ibkickinit/schindler-clone/clockInfo.txt

-------------------------------------
| Tool Version : Vivado v.2025.2
| Date         : Sun Jun  7 10:25:25 2026
| Host         : justin-Yoga-7-14ITL5
| Design       : design_1
| Device       : xc7z020-clg400-1--
-------------------------------------

For more information on clockInfo.txt clock routing debug file see https://support.xilinx.com/s/article/000035660?language=en_US
