ibkickinit/schindler-clone/00-index.md

# Schindler 2.0 — 00 Index

**Status:** ACTIVE — HD pipeline development on Zybo Z7-20
**Type:** Personal venture
**Code location:** `_PROJECTS/Schindler-2.0/` (this folder, repo at root)
**GitHub:** `ibkickinit/schindler-clone` *(rename to `schindler-2` planned later)*

## What this is

FPGA-based hardware project to drive video to legacy CRTs at film cadences (24/30 fps), with the broader scope of acting as a general broadcast-grade HD signal processor. Spiritual successor to the Cal Media MVPHD-24 device — replicating that workflow with modern FPGA tech, and extending to HD pipeline + sync conversion + per-CRT color profiles + RF modulator (Pro) for period sets.

The mission: keep heritage display gear functional in modern production workflows, where 24fps cinema cadence needs to drive into displays designed for older signal standards.

## Two SKUs, one electronics design

**One internal electronics design — two packaging variants.** Mini and Pro share the same carrier PCB, the same TE0720 SOM, the same FPGA HDL, the same PetaLinux control plane. They differ in chassis form factor, front-panel hardware, rear-panel I/O complement, and carrier stuffing.

- **Mini v1** — first shipping SKU. Half-rack 1RU chassis. Mono OLED + tactile switches front panel. Subset of stuffing (no SDI, no RF modulator, no dual SYNC OUT, no per-connector LEDs, no rear LCD). Indicative retail $1,500–2,500; parts cost ~$572.
- **Pro v2** — full-rack 1RU chassis. NHD-2.9 color TFT + RP2040 + BT817Q EVE mezzanine front panel. Full silicon stuffing. Indicative retail $2,500+; parts cost ~$816. Gated on Mini selling.

See [`docs/packaging-skus.md`](docs/packaging-skus.md) for SKU stuffing matrix + chassis detail.

## Doc structure

- [`docs/01-spec.md`](docs/01-spec.md) — SSOT for internal electronics architecture and feature set. Applies to both SKUs.
- [`docs/packaging-skus.md`](docs/packaging-skus.md) — Mini vs Pro packaging differences (chassis, front panel, rear panel I/O, stuffing variants).
- [`docs/dev-roadmap.md`](docs/dev-roadmap.md) — SSOT for active development arc and deferred work. **Read this first** to know what's being built right now.
- [`docs/01-spec-changelog.md`](docs/01-spec-changelog.md) — dated decision history.
- [`docs/signal-flow.md`](docs/signal-flow.md) — Mermaid block diagrams (video signal path, sync subsystem, control plane).
- [`docs/panel-layout.md`](docs/panel-layout.md) — Pro panel layout. Mini layout in `packaging-skus.md`.
- [`docs/bom-v1.md`](docs/bom-v1.md) — BOM with Mini/Pro stuffing variants.
- [`docs/ui-menu.md`](docs/ui-menu.md) — Pro UI menu hierarchy. Mini UI hierarchy authored when Mini PetaLinux UI work activates.
- [`docs/mvphd-comparison.md`](docs/mvphd-comparison.md) — MVPHD-24 feature comparison + gap analysis.
- [`docs/rf-modulator-subsystem.md`](docs/rf-modulator-subsystem.md) — RF modulator detail (Pro feature).
- [`docs/opamp-stage.md`](docs/opamp-stage.md) — output op-amp design.
- [`docs/r2r-dac.md`](docs/r2r-dac.md) — R-2R DAC perfboard reference (Zybo bench).
- [`docs/schindler-playbook.md`](docs/schindler-playbook.md) — development narrative.
- [`docs/Hardware/`](docs/Hardware/) — archived future-evaluation hardware (Smart Artix, Smart Zynq SL, TE0712, TinyZynq) — **NOT** on the active dev path. Preserved for archival reference.

## Active development arc

Building **HD pipeline top-down** on Zybo Z7-20:

```
Phase A: HDMI passthrough        (next up)
Phase B: VDMA frame buffer
Phase C: Polyphase scaler
Phase D: Frame rate conversion
Phase E: Color pipeline
Phase F: Geometry warp
Phase G: Re-attach analog terminal encoders (Phase 2 HDL plugs back in here)
```

Migration from Zybo to TE0720 production target comes after the HD pipeline validates. See [`docs/dev-roadmap.md`](docs/dev-roadmap.md) for current status, deferred work, and forward-looking work.

## Recently completed

**Phase 2 first-light** on Zybo Z7-20 + R2R DAC perfboard:
- Monochrome NTSC composite at 24.000 fps exact — scope-validated
- `hdl/vid_timing.v` + `hdl/vbi_gen.v` + `hdl/sample_gen.v` validated
- `hdl/chroma_gen.v` written + integrated + builds clean; chroma burst bench verification deferred per HD-pipeline-first priority shift

## Hardware status

- ✅ **Digilent Zybo Z7-20** — active dev platform
- ✅ R-2R DAC perfboard + op-amp output stage
- ✅ Phase 2 NTSC composite HDL on bench, scope-validated through monochrome

**Inbound 2026-05-13:**

*Digilent order (Pmod accessories for Arty S7-25 ecosystem — FedEx 487403305746):*
- Pmod OLED 128×32 mono (410-222) — **Mini front-panel UI prototype**, exact display class as production
- Pmod OLEDrgb 96×64 color (410-323) — Pro UI flow / menu hierarchy prototyping at small scale
- Pmod ENC rotary encoder ×2 (410-117) — **Pro dual-encoder firmware prototyping**
- Pmod SWT 4 slide switches (410-083) — UI input testing
- Pmod R2R (410-165) — backup / cleaner R-2R DAC vs perfboard
- Pmod TPH2 test point header (410-135) — debug measurement
- Pmod Cable Kit + 6-pin splitter (240-021-2) — Pmod fan-out wiring
- Pmod VGA (410-345) — prototype platform for VGA OUT terminal if banked (currently in `01-spec.md` § 21 open questions)

*HelloFPGA order (China — bench eval / inventory):*
- Smart ARTIX Development Board V1.3 — inventory (archived in `docs/Hardware/SmartArtix/`)
- Smart ZYNQ 7020 Minimum System V1.3 (Smart Zynq SL) — inventory (archived in `docs/Hardware/SmartZynq/`)
- **LT8619C chips ×5** — production-quantity HDMI-input silicon stockpile
- LT8619C HDMI-to-RGB demo board — second LT8619C-EVB

*Pending order:*
- **Riverdi RVT43HLBFWN00** (4.3" 480×272 EVE4 intelligent display with BT817Q + flash on board, ~$62) — Pro mezzanine EVE toolchain dev platform. Replaces earlier ME817EV consideration; cheaper, more complete, matches production BT817Q spec exactly. Stock-pending at Mouser / DigiKey; not time-critical.

Net effect: enables a **parallel front-panel UI prototyping arc** on Arty S7-25 + Pmod OLED/OLEDrgb/ENC that doesn't block on Zybo HD pipeline phases A-G, and a parallel **EVE toolchain learning arc** once RVT43HLBFWN00 arrives.

**Future-evaluation hardware** (procured but NOT the active dev plan — bench eval / parts inventory only):
- Trenz TE0720-04-31C33MA SOM, TE0703-07 dev carrier, EVAL-ADV7393EBZ, LT8619C-EVB, ADV7280, ADV7393, LTC6912, AD9204, encoders, op-amps, BNCs (various 2026-05-10 / 11 procurements)
- Digilent Arty S7-25 — toolchain learning + Spartan-7 comparison only
- Smart Artix V1.3 / Smart Zynq SL V1.3 / TE0712-02 / TinyZynq — evaluation archive (`docs/Hardware/`)

The TE0720 is the **production-target SOM**; bench dev happens on Zybo Z7-20 (same Z-7020 silicon family). Production migration after HD pipeline validates.

## Operating principle (code in vault)

`.git/` syncs to Dropbox cloud. NEVER delete `.git/` from cloud — propagates to local and destroys repo. See `_PROJECTS/NovaTool/00-index.md` for full rationale on code-in-vault.

## Migration status

- [x] Migrated from `~/schindler-clone/` to `_PROJECTS/Schindler-2.0/` (2026-05-06)
- [x] Remote URL cleaned (no embedded PAT)
- [x] Two-SKU strategy banked (Mini v1 / Pro v2) (2026-05-12)
- [x] Doc tree consolidated: mini-spec + carrier-board absorbed into 01-spec; packaging-skus + dev-roadmap created (2026-05-13)
- [ ] Rename GitHub repo: `schindler-clone` → `schindler-2`
- [ ] Document FPGA-specific `.dropboxignore` patterns once active build artifacts appear

## Naming history

- Working title: `schindler-clone` (placeholder during initial setup)
- Final name: **Schindler 2.0** (chosen 2026-05-06; emphasizes spiritual successor framing rather than direct clone)
