ibkickinit/schindler-clone/docs/part-lock-2026-06-12.md

# Schindler 2.0 — Production Part-Lock Pull-Sheet (Pro)

**Generated:** 2026-06-12 · **Source of truth:** [`bom-v1.md`](bom-v1.md) (this is a flat procurement view of it — if they disagree, the BOM wins). Qty = **per Pro unit**; ×100 for the production run. Vendor assumed **DigiKey / Mouser** unless noted. Status: 📋 = locked, not yet ordered; ✅ = on order/received; 🔬 = bench eval.

## Active silicon

| Ref | MPN | Mfr | Qty | Pkg | Status |
|---|---|---|---:|---|---|
| Zynq SoM | TE0720-04-62I33MA | Trenz | 1 | SoM | 📋 |
| HDMI ESD/lvl ×2 | TPD12S016PWR | TI | 2 | — | ✅ |
| HDMI RX | LT8619C | Lontium | 1 | — | ✅ |
| Analog decoder | ADV7280AWBCPZ-M-RL | ADI | 1 | — | ✅ |
| Analog enc/DAC | ADV7393BCPZ-REEL | ADI | 1 | — | ✅ |
| Video buffers | LMH6643MAX/NOPB | TI | 3 | MSOP-8 | ✅ (2 out + 1 sync) |
| SDI RX (Pro) | GS3470 | Semtech | 1 | — | 📋 |
| SDI TX (Pro) | GS2962 | Semtech | 1 | — | 📋 |
| Genlock PGA | LTC6912CGN-2#PBF | ADI | 1 | — | ✅ |
| Genlock ADC | AD9204BCPZ-20 | ADI | 1 | — | ✅ |
| SYNC1 DAC | AD9742 | ADI | 1 | — | 📋 |
| Clock gen ×2 | Si5351A-B-GTR | Skyworks | 2 | MSOP-10 | 📋 (genlock + RF) |
| UI MCU ×2 | RP2040 | Raspberry Pi | 2 | QFN-56 | 📋 (genlock + mezz) |
| QSPI flash ×2 | W25Q128JVSIQ | Winbond | 2 | SOIC-8 | 📋 |
| Term switch | TS5A23159 | TI | — | — | 📋 (input/genlock) |
| Graphics ctrl | BT817Q | BridgeTek | 1 | — | 📋 |
| LED drivers | TLC59116F | TI | 3 | — | 📋 |
| WiFi/BT module | LWB5+ | Laird | 1 | module | 📋 |

## Power

| Ref | MPN | Mfr | Qty | Status |
|---|---|---|---:|---|
| IEC + filter + fuse | FN9260B-6-06 | Schaffner | 1 | ✅ |
| Mains fuse | 0213002.MXP (2 A T) | Littelfuse | 1 | 📋 |
| PSU | LRS-50-12 | Mean Well | 1 | ✅ |
| Protection eFuse | TPS26600 | TI | 1 | 📋 |
| Power monitor | INA226AIDGSR | TI | 1 | 📋 |
| Soft-power ctrl | LTC2954ITS8-1 (TSOT-23) | ADI | 1 | 📋 |
| 5 V / 3.3 V buck | LMR33640ADDAR | TI | 2 | 📋 |
| 1.2 V buck | TLV62568DBVR | TI | 1 | 📋 |
| 1.8 V analog LDO | TPS7A2018PDBVR | TI | 1 | 📋 |
| Clean analog POL LDO | ADP7142 (adj) | ADI | ~3 | 📋 (per ADC/decoder, sized at schematic) |

## Connectors

| Ref | MPN | Mfr | Qty | Status |
|---|---|---|---:|---|
| BNC 75 Ω R/A PCB | 73101-0120 | Molex | 14 | 📋 |
| HDMI Type A R/A | 10029449-001RLF | Amphenol ICC | 2 | 📋 |
| RJ45 Gig magjack | JXD1-0001NL | Pulse | 1 | 📋 |
| USB-C 2.0 R/A | USB4085-GF-A | GCT | 1 | 📋 |
| USB-C ESD | TPD4S014DBVR | TI | 1 | 📋 |
| RP-SMA bulkhead | CONREVSMA001 | Linx | 2 | 📋 |
| Antenna (dual-band) | ANT-DB1 | Linx | 2 | 📋 — verify vs LWB5+ grant |
| PSU header | 0039291028 (+ 5557-02R hsg) | Molex | 1 | 📋 |
| F-connector (RF bd) | 82-4421-RFX | Amphenol RF | 1 | 📋 |

## Panel / UX

| Ref | MPN | Mfr | Qty | Status |
|---|---|---|---:|---|
| Front TFT | NHD-2.9-376960AF-ASXP | Newhaven | 1 | 📋 |
| TFT backlight boost | TPS61040 | TI | 1 | 📋 |
| Rear LCD | NHD-1.5-240240AF-CSXP | Newhaven | 1 | 📋 |
| Encoders | EC11E18244AU | Alps | 2 | ✅ |
| Tactile buttons | PTS645SM43SMTR92LFS | C&K | ~7 | 📋 |
| Power button | E-Switch PV6 (illum. mom.) | E-Switch | 1 | 📋 |
| Status LEDs | L-3VEGW-CA (3 mm bi-color CA) | Kingbright | 21 | 📋 |

## RF daughter board (Pro)

| Ref | MPN | Mfr | Qty | Status |
|---|---|---|---:|---|
| AM modulator | ADL5391ACPZ-R7 | ADI | 1 | 📋 (bench 🔬) |
| RF amp | ERA-3SM+ | Mini-Circuits | 1 | 🔬 (5 on order) |
| Shield can frame | MS643-10F-NS | Masach | 1 | 📋 |
| Shield can cover | MS643-10C-NS | Masach | 1 | 📋 |
| Feedthrough (DC) | NFM21PC104R1E3D | Murata | 2 | 📋 |
| Feedthrough (I²C) | NFM21CC102R1H3D | Murata | 2 | 📋 |
| Series ferrite (opt) | BLM21PG600SN1D | Murata | 2 | 📋 |
| Output trims | 3224W (SMD multiturn) | Bourns | 2 | 📋 |
| RF ESD | PESD3V3L1BA | NXP | 1 | 📋 |
| (Si5351 + 25 MHz xtal, u.FL jack + cable, 6-pin header — see RF BOM) | | | | |

## Thermal / mechanical

| Ref | MPN / spec | Mfr | Qty | Status |
|---|---|---|---:|---|
| SoM heatsink | 33337 | Trenz | 1 | ✅ |
| Fan | NF-A4x20 PWM | Noctua | 1 | 📋 |
| SoM gap pad | silicone, ~1 mm | generic | 1 | 📋 |
| Chassis | 1U full-rack extruded | Hammond | 1 | 📋 (model at mech) |
| Front/rear panel | milled aluminum | Front Panel Express | 1 ea | 📋 (from `panel-layout.md`) |
| Standoffs / screws / M4 earth stud | M3 brass / M2.5 / M4 | generic | set | 📋 |

## Bulk passives (sized at schematic — not individually pre-locked)

- Decoupling: 0.1 µF + 10 µF per rail/IC (X7R / X5R).
- Input front-ends: BAV99 clamp + TVS, 75 Ω term, AC-couple + anti-alias R/C per CVBS/component/REF input.
- 12 V bulk: 3× Murata GRM32 22 µF 25 V X7R.
- RF bandpass: 5th-order Butterworth — Coilcraft 0805CS-class L + C0G C (~9 parts), values bench-tuned.
- 50→75 Ω MLP: 43 Ω + 82 Ω 1%; audio combiner: 3× R.
- LTC2954 timing (ONT/PDT) caps, PB R-C; eFuse OVP/UVLO/ILIM/dVdt resistor set.

## Still open (deliberate — not a part gap)

- **FCC emissions class** → defaulting **Class B** margin; relax to A only if filter margin wanted. Pre-layout call.
- **Antenna final MPN** → confirm Linx ANT-DB1 against the LWB5+ FCC grant antenna list before order.
- **Production knob** → post-UX-eval; shaft-mount, no netlist impact.
- **Procurement-final suffixes** → BNC packaging tray/reel, E-Switch PV6 color/voltage, at order time.
