ibkickinit/schindler-clone/docs/warp-engine-real-geometry-findings.md

# Warp engine — real-geometry findings (the TB green does NOT mean real-time at 1080p)

> **RESOLVED 2026-06-07 — the warp engine is now real-time at 1080p.** Three enhancements (below)
> close the gap; `pg_warp_real_tb` (8-way/NTILE=1024, PD=DREQ=64, LEAD=32768) clears rot20/shrink/aniso
> with underruns=0 over the full 1280×720 frame; rot45 has a single cold-start underrun (cn=3, benign).
> No dual-clock fill. **The resolution is in §"Resolution" at the bottom; the analysis below is the
> investigation that found the bottlenecks.**

**Date:** 2026-06-07. **Re:** confirming the real-time LEAD at the production geometry before sizing
cache ways (the "confirm the real lead first" decision).

**TL;DR:** I built a full real-geometry gate (`sim/pg_warp_real_tb.v`, 1280×720 ← 1920×1080, 720p60
raster) and ran shrink 1.5× (the fill/lead driver). **It is NOT real-time** as architected — and the
reason is not the fill rate. The TB (`pg_warp_dma_tb`, 1/5 scale) passes 4/4 because its small frame
fits the cache entirely and gets a disproportionate V-blank warmup head-start; **neither holds at full
scale.** Two real bottlenecks the TB masked: **(1) no LRU eviction**, and **(2) prefetch feed depth.**

## The measurements (real geometry, shrink 1.5×, collected of 921600)

| cache | PD / DREQ | LEAD | collected | note |
|---|---|---|---|---|
| 4-way / 512 | 16 / 16  | 8k–49k | **5%** | LEAD has no effect; capacity-bound |
| 16-way / 2048 | 16 / 16  | 16k–131k | **25%** | LEAD still no effect; PD-bound |
| 16-way / 2048 | 64 / 64  | 65k | 23% | deeper PD *worse* — still evicting |
| 16-way / **16384** (no eviction) | 16 / 16 | 65k–262k | **62%** | eviction removed → big jump |
| 16-way / 16384 | 64 / 64  | 131k | **85%** | now PD/lead start working |
| 16-way / 16384 | **128 / 128** | **262k** | **94%** | trending to real-time, impractical cost |

Fill-path health at the stalling point (16-way/2048, PD16, LEAD65k): **clk/tile = 96 (= the target 2.67
px/clk — the gap-free fill is at its design rate), but beat_duty = 0.20, work_frac = 0.34** (the DMA has
a pending fetch only 34% of the time). So the DMA is *starved*, not slow.

## Why — two coupled bottlenecks the small TB hid

1. **No LRU eviction.** My victim is free-way-first with a round-robin fallback only when a set is
   *full*. That never *proactively* recycles dead tiles — they sit valid until the set fills, then RR
   evicts arbitrarily (sometimes a still-live tile). The TB never hit this (its frame fits the cache, so
   eviction never happens). At 1080p, shrink touches ~8100 tiles while its *live* working set is only a
   few hundred; with LRU + worst-set-live ≤ ways, a modest cache would hold the live set indefinitely
   and never evict a live tile. Without it, the cache fills with dead tiles and thrashes — which is why
   "no eviction" (NTILE=16384) jumped shrink 25%→62%, and why more ways = more rows-before-stall.

2. **Prefetch feed depth.** Even with eviction removed, PD=16 caps shrink at 62%; PD=128 + a very deep
   lead reaches 94%. The fill is serial (tile_dma fills one tile at ~96 clk), so covering shrink's
   ~120-tile tile-row-crossing burst needs many fills queued and a deep lead to pre-fill it. The TB's
   24-tile burst hid this (16 sufficed). The *rate* is adequate (2.67 px/clk × frame ≈ 3.3M px ≫ the
   2.07M px shrink reads/frame, 1.6× headroom) — the problem is keeping the DMA continuously fed, which
   the current lead-gated race-then-idle prefetch does not.

## What this means

- **The reviewer's bet (2.67 px/clk + non-thrashing cache + deep lead) holds on *rate* but the
  "non-thrashing cache" needs real LRU, not RR**, once eviction is mandatory (it never is in the TB).
  And the prefetch needs more pacing/depth than the TB implied.
- **Dual-clock fill is probably still NOT the answer** — the rate has 1.6× headroom; the loss is feed +
  eviction, not bandwidth. Halving fill time would ease the burst-lead pressure but doesn't fix the
  underlying feed/eviction inefficiency.

## Recommended next architecture step (for discussion before building)

1. **Per-set tree-PLRU** victim (4/8-way). With worst-set-live ≤ ways, PLRU never evicts a live tile →
   a modest cache (NTILE 512–1024) holds shrink's live working set with no thrash. This is the big one.
2. **Re-measure the real-time lead/PD with PLRU** — expect the impractical PD=128 / 200-row-lead to drop
   sharply once the cache stops thrashing, because the prefetch no longer wastes fills re-fetching
   evicted tiles. Only then size ways (8-way for rot20's lead-aware 5–7, per
   `tools/warp_lead_assoc.py`).
3. If PLRU + reasonable PD still can't feed the DMA continuously, revisit prefetch pacing (issue rate
   matched to fill capacity) before reaching for dual-clock fill.

## Status of the assigned fill rework

The fill rework itself is **done and correct** — `pg_warp_dma_tb` passes all four transforms
(underruns=0, bit-err=0), the gap-free fill hits 96 clk/tile, multi-outstanding works. What this
real-geometry gate adds is: **the TB is necessary but not sufficient** — it cannot exercise eviction or
the full-scale burst, and both bite at 1080p. The cache (`pg_tilecache_rt2`) now takes a `WAY` parameter
(4 default, plumbed through `pg_warp_engine`) so the PLRU + 8-way work has a clean home, and
`pg_warp_real_tb.v` is the gate to drive it.

## Resolution (2026-06-07) — three enhancements make it real-time at 1080p

Each was found by the measurements above, applied in order, and re-swept on `pg_warp_real_tb`:

1. **FIFO-by-fetch eviction** (`pg_tilecache_rt2`, replaces RR fallback). Per-slot fetch-sequence
   stamp; the victim is the **oldest-fetched non-reserved** way (free-way-first, then FIFO). Because the
   prefetch fetches in the consumer's future-access order, the oldest-fetched resident tile is the one
   the consumer already passed = dead. A modest cache now recycles dead tiles continuously instead of
   filling up and thrashing. **Real-geometry shrink at 4-way/512: 5% → 62%.** No per-access update
   (FIFO ≈ LRU for the streaming prefetch order), so it's cheap.

2. **Wide gearbox** (`pg_tile_dma`). The receiver drained ≤3 px/clk with `beat_ready=nbits<=64`; since
   64b/beat isn't a multiple of 24b/px, the accumulator settled at a low equilibrium where `navail` was
   usually 2, throttling the beat rate to ~1.6 px/clk (`duty_when_work=0.60`) — just under shrink's
   ~1.67 px/clk need (hence the 94% ceiling). Fix: 4 px/clk drain + permissive `beat_ready=nbits<=96`
   (200-bit acc) so `navail` stays 3–4 and the receiver sustains the full 2.67 px/clk. **This is what
   took shrink from 94% to 100%** and dropped the PD need from 128 to 64.

3. **Deeper feed** — `PD` is now a parameter (default 16, **64 for the real geometry**) with matching
   `DREQ`. Keeps the DataMover continuously fed across the bursty miss pattern (the ~120-tile tile-row
   crossing). `work_frac` 0.34 → 1.00.

### Validated production config (real geometry)

| param | value | why |
|---|---|---|
| WAY | **8** | lead-aware worst-set-live ≤8 at LEAD=32768 (rot20=7, aniso=6); 4-way thrashes |
| NTILE | **1024** | 8-way × 128 sets (keep 128 sets — the hash needs them; ~96 RAMB36) |
| PD / DREQ | **64** | covers the ~120-tile crossing burst feed (PD=16 caps at 62%, 32 at ~80%) |
| LEAD | **32768** | shrink real-time needs it; 8-way still holds (max worst-set-live=7). 65536 pushes aniso to 9 → would need 16-way |
| victim | FIFO-by-fetch | non-thrashing eviction |
| gearbox | 4 px/clk / nbits≤96 | sustains 2.67 px/clk |

**LEAD is the binding cross-constraint:** shrink wants it deep, aniso's lead-aware count grows with it.
LEAD=32768 is the sweet spot where shrink is real-time AND all four stay ≤8-way. (rot45's lone cn=3
cold-start underrun is a warmup transient — the cache persists across frames in the genlocked system, so
it occurs at most once at power-on, on the top-left pixel.)

### Cost vs the small-TB config
- Cache BRAM ~2× (NTILE 512→1024). Pending/request FIFOs PD/DREQ 16→64 (logic, not BRAM). Wider gearbox
  acc (136→200b) + FIFO seq array (NTILE×16b) — modest.
- **No dual-clock fill** (the reviewer's hoped-for outcome): the 2.67 px/clk rate is sufficient once the
  gearbox actually sustains it and eviction stops wasting fills.

### Still open
- rot45 cold-start pixel (benign; could be cleaned with cross-frame prefetch warmup in firmware).
- The PD=128 regression (collapses vs PD=64) is unexplained — irrelevant since 64 is the operating
  point, but worth understanding before pushing PD higher.
- FIFO ≈ LRU holds for streaming/rotation here; a pathological revisit pattern could want true LRU. Not
  observed in the four transforms.

### Cold-start is power-on-once (not per-coeff-change) — confirmed by HDL inspection
The cache (`pg_tilecache_rt2`) has **no `sof`, no flush, no invalidate-all**: `vld` is cleared only
per-slot on evict and set per-slot on fill. `sof` resets only the prefetch's `lead_cnt` (benign — with a
warm cache the prefetch re-establishes its lead through hits, no refetch). Coeffs latch frame-atomically
inside `pg_affine`; on a live geometry change the FIFO age (global `fseq`) recycles the old-geometry
tiles as the new working set arrives — a smooth working-set shift, **not** a cold-start. So the rot45
cn=3 transient occurs at most once at power-on/reset, on the top-left pixel — it does NOT recur per frame
or per zoom/rotate/pan adjustment. (A very large single geometry jump could cost a one-frame transient as
the whole working set turns over, but not a persistent twinkle during incremental tuning. A mid-stream
coeff-change sim would be the definitive confirmation — good follow-up.)

### Timing: pending-availability cone collapsed from PD-deep to associativity-deep
The multi-outstanding pending check was refactored from a PD(64)×4 = 256-comparator FIFO scan to a
single `(vld||rsv)&&tag` lookup over a set's WAY ways (write the tag at ISSUE with rsv=1, so resident
and in-flight are the same lookup): **WAY(8)×4 = 32 comparators**, bounded by associativity not lead
depth, and it scales if PD grows. Removes the cone rather than pipelining it. Both gates re-verified
identical. The consumer gather tag lookup (the original in-context WNS −3.5 path) is now 8-way; the build
will say whether it needs the reserved tag-lookup pipeline stage.

## Fit (2026-06-07) — 8-way/1024 does NOT fit the 7020; per-geometry LEAD does

The in-context build at the real-time config (8-way / NTILE=1024) **synthesized but failed impl DRC on
resource over-utilization, not timing**: `pg_re_0` (the warp engine) alone = **192 RAMB36 > 140
available**; total LUT 72580 / 53200. The cache is 4 banks × NTILE·64 × 24b; at NTILE=1024 that is
192 RAMB36 by itself. **The production target (TE0720) is also a Zynq-7020** (−2 silicon, same 140 BRAM)
— so 8-way/1024 fits neither the dev board nor the product. Removing the debug ILAs (~32 BRAM) is not
enough.

**Root of the 8-way requirement, and the fix.** 8-way came from the lead-aware worst-set-live at a
*single global* LEAD=32768 (rot20=7, aniso=6). But rot20 and aniso don't *need* a deep lead — only
downscale (shrink) does. A deep global lead over-inflates the easy transforms' per-set occupancy. With a
**per-geometry LEAD** — the firmware sets a shallow lead for rotation and a deep one for downscale —
every transform is real-time at a lead where worst-set-live ≤ 4 (validated on `pg_warp_real_tb`,
generous cache so capacity isn't the variable):

| transform | minimal real-time LEAD | worst-set-live @ that lead |
|---|---|---|
| rot20 | 1280 | 4 |
| rot45 | ~4096 | 2 |
| shrink 1.5× | 24576 | 3 |
| aniso (rot30+1.5×H) | ~10240–12288 | 4 |

Max worst-set-live across the per-geometry leads = **4 → 4-way / NTILE=512 (~96 RAMB36) fits the 7020.**
The cache only ever sees one transform's pattern at a time (at that transform's lead), so the global
lead-aware table that demanded 8-way no longer applies.

**LEAD must become a runtime register** (firmware-written per geometry, deep ∝ downscale factor) instead
of a build parameter — a small follow-up (the engine already takes LEAD as a param; expose it as a
GPIO-driven port). Cache persistence + frame-atomic coeff latching mean changing LEAD with the geometry
is a smooth working-set shift (same as the cold-start analysis above). Until then, a single fixed LEAD
will thrash whichever transform's lead it doesn't match at 4-way.

**Build status:** BD config set to 4-way/NTILE=512/PD=64/DREQ=64 (LEAD placeholder); rebuilding to confirm
the device holds the warp engine (BRAM ✓ expected ~96, LUT TBD) and timing closes. Per-geometry LEAD is
the remaining real-time mechanism (firmware).

### Cost ledger (4-way/512, the fitting config)
- Cache ~96 RAMB36 (4 banks × 512·64 × 24b). Fits 140 with room for VDMA/scaler/output once debug ILAs
  are dropped.
- LUT: 8-way build was 72580 (36% over). 4-way halves the lookup/vict/availability/seq logic; PD=64
  FIFOs + wide gearbox unchanged. Rebuild will say if it now fits 53200.
- No dual-clock fill. Single DataMover. Set-index unchanged.

### Fit round 2 (4-way/512): BRAM clears, now SLICES (LUT/FF) over by ~24%
4-way/NTILE=512 cleared the BRAM wall (cache ~96 RAMB36, no BRAM DRC error). Impl now fails at **place**
on slices: **13456 required / 10893 available (~24% over)** — LUT/FF, still not timing. Per-IP LUTs
(synth OOC):
- `pg_re_0` (warp engine) = **29723 LUTs** — dominant. PD=64/DREQ=64 FIFOs, the 200-bit wide gearbox
  (variable barrel shifters), the 512×16b `seq` array + 4-way age-argmax, the `(vld||rsv)&&tag`
  availability (4×4×24b), 2× affine DDAs, bilinear, `setf` multiplies.
- 3 system ILAs = ~10549 LUTs (`ila_s2mm_axi` 5218 + `ila_scaler_out` 2799 + `ila_mm2s_out` 2532),
  plus `ila_pixclk`/`ila_refclk` — **all debug-only.**
- VDMA 2982, scaler mem 2297, v_tc_rx/tx 1522/1327, etc.

**Closing the ~2563-slice gap (well-scoped, next session — verify each with a rebuild):**
1. **Drop the debug ILAs** (gate the `system_ila` cells + their probe nets behind an `ILA_EN` flag in
   `build_phase_b.tcl`, default off for warp builds): ~10549+ LUT ≈ ~1300–1500 slices. Closes roughly
   half. Low risk but touches the BD (must remove probe connections cleanly).
2. **PD/DREQ 64→32** if shrink real-time tolerates (re-check on `pg_warp_real_tb`): halves the pf_slot
   (64×9b) + tile_dma rq (64×24b) FIFOs.
3. **Trim `seq` width** 16→~10 bits (age only needs to order the live working set) and/or move it to
   LUTRAM/BRAM: saves ~512×6 FFs off the slice count.
4. If still short, narrow the gearbox barrel shifters (the 200-bit acc / variable 96-bit shifts are
   LUT-heavy) — but the wide gearbox is load-bearing for shrink's 2.67 px/clk, so re-verify real-time.

ILAs (1) + PD↓ (2) + seq↓ (3) should clear ~24% comfortably. None affects the validated datapath/
real-time behaviour; they're area trims + debug removal. After a clean place, read post-route WNS.

## Fit round 3 (4-way/512 + NO_ILA): FITS and routes — but WNS −28.76 (prefetch cone)
Gating the 3 debug ILAs (NO_ILA=1) recovered enough slices: the 4-way/NTILE=512/PD=64 warp build
**places, routes, and writes a bitstream on the 7020** (BRAM ✓ ~96, slices ✓). WHS=+0.0096 (hold ok).
But **WNS = −28.757 ns** at the 74.25 MHz pixel clock (13.468 ns period).

**Failing path (single dominant cone):**
`pg_re_0/.../u_tc/px__reg` (prefetch coord) → `u_tc/tag_reg[241]` (tag write). **41 logic levels, 41.5 ns**
(logic 10 ns / route 31.5 ns), CARRY4=11 (the `setf` `*13`/`*7` multiplies) + 12×LUT6 + MUXF7/8. This is
the **entire prefetch issue decision computed combinationally in one cycle**: px_ → ppx/ppy neighbours →
`setf`/`tidf` for 4 tiles → `(vld||rsv)&&tag` availability over the ways → first-unavailable select →
`vict` age-argmax → `ua_slot` → tag/slot write. The earlier in-context −3.5 was this same cone at 4-way
*without* the tag-at-issue + FIFO-vict additions; those (correct, and needed) deepened it to 41 levels.

**Fix (next session — the prefetch has slack, leads the consumer by LEAD, so pipeline latency is free):**
Pipeline the prefetch issue path into ~3–4 register stages, e.g.
 1. px_ → register ppx/ppy (4 neighbour coords) + their `setf`/`tidf` (the multiply — isolate it).
 2. register the `(vld||rsv)&&tag` availability result (av00..av11) per tile.
 3. register all_av + the first-unavailable `ua_*` (set/way/tid) selection (incl. `vict`).
 4. issue (tag/rsv/pf write).
**Hazard:** with pipeline latency, a tile issued at cycle T is not visible in the tag/rsv arrays for k
cycles, so cycles T+1..T+k could re-issue it (the same class as the original pend_has bug). Add a small
"recently-issued" bypass — a k-deep register of the last ua_slot/ua_tid checked in the availability —
or stall the coord-advance until the issue retires. The consumer gather lookup (looka→baddr→BRAM) is a
*separate*, shorter path and was not the worst; check it after the prefetch is pipelined.

Note the path is **76% route** (31.5 of 41.5 ns) — 41 logic levels scattered across the die. Pipelining
cuts both the logic depth and the routing (shorter nets per stage). This is careful hazard-prone work;
recommended for a fresh session per the build/WNS boundary.

**State at handoff:** fit + real-time both solved (all four real-time at 4-way/512 with per-geometry
leads: rot20@1280, rot45@4096, shrink@24576, aniso@12288 — rot45 1 cold-start px). Bitstream exists but
is non-functional at speed until the prefetch cone is pipelined. Build log: build_logs/warp_build_noila.log.

### Next-session pipelining plan (REFINED — feedforward vs state-dependent split)
The 41-level cone is two different animals; only one is hazard-prone. Do them in this order:

**1. Pipeline the FEEDFORWARD PREFIX first — hazard-free, biggest level reduction.**
   prefetch coord (px_) → ±1 neighbour coords → `setf` `×13`/`×7` multiplies → set indices + tile-ids
   (ps00..11, pt00..11). This depends ONLY on the coords (the affine DDA produces them deterministically
   ahead of time), touches no mutable cache state, so register it into ~3 stages with **zero re-issue
   hazard**. This is probably the bulk of the 41 levels (the two multiplies + neighbour math, CARRY4×11).
   Keep `lookup → reserve → write` as a single ATOMIC cycle.

**2. Re-time. If the atomic suffix now closes in one cycle, you are DONE — no hazard work at all.**
   Because the reservation still happens in the same cycle it reads state, the next prefetch coord sees
   it. Most likely outcome once the multiplies are staged out.

**3. ONLY IF the atomic suffix is still too deep, split it — "reserve immediately, compute pipelined":**
   - The `rsv` slot-reservation bit MUST be set combinationally at issue so it is visible next cycle —
     that single-cycle reservation prevents BOTH double-issue AND double-victim (two fills racing for one
     slot — the nastier corruption).
   - Pipeline only the heavy compute behind it (availability read, first-unavailable select, `vict`
     age-argmax).
   - Add a small **k-deep recently-issued shift-register (k≈4), checked combinationally** = a k-entry CAM
     covering the read-side shadow (the k cycles where a just-issued tile isn't yet in the arrays). This
     is far cheaper and safer than a coord-advance stall — a stall would throttle the prefetch and risk
     reintroducing the lead/starvation just solved.
   - **Re-run BOTH sim gates** after this — `pg_warp_dma_tb` (underruns=0, bit-err=0) AND
     `pg_warp_real_tb` (real-time, no re-issue starvation) + the lead-aware check. This re-verify is the
     part that must not be done tired.

Then: check the consumer gather path (looka→baddr→BRAM — separate, shorter) timing; rebuild; read WNS.

### ⚠️ NO_ILA is a load-bearing build constraint
The warp build fits the 7020 **only with the 3 debug ILAs gated off** (`NO_ILA=1`). Carry this into
bench/debug: you lose on-chip ILA visibility (scaler_out / mm2s_out / s2mm_axi pixel-stream capture)
exactly in the warp build where you might want it. If ILA visibility is needed for a warp bench session,
something else must give (smaller cache for that debug build, or fewer ILA slots).

### Bitstream status
`build_logs/warp_build_noila.log` produced a routed bitstream, but with WNS −28.76 it is **NON-FUNCTIONAL
at 74.25 MHz — do not bench it.** It only proves fit (place+route+BRAM+slices). A functional bitstream
needs the prefetch pipelining above + a clean WNS≥0 build.

### Fit round 4 (prefetch feedforward pipelined): WNS −28.76 → −20.27, suffix is the residue
Step 1 (register the feedforward — neighbour coords + setf *13/*7 multiplies into stage 2, suffix atomic;
commit `<feedforward>`) moved WNS from −28.76 to **−20.27** and is sim-verified (small TB 4/4 bit-exact;
real-geometry shrink@24576 / aniso@12288 / rot20@1280 real-time). New worst path:
`u_tc/ps01_reg → u_tc/tag_reg`, **32 logic levels / 33.3 ns (CARRY4=7, LUT6=9, MUXF7×4/MUXF8×2), 78%
route.** The setf is gone (source is the registered ps). The residue is the state-dependent SUFFIX:
`ps(reg) → (vld||rsv)&&tag availability over WAY ways → first-unavailable select → vict age-argmax →
tag/rsv write`.

**To close the remaining ~20 ns (next session — the hazard-prone part):**
1. **Replace the `vict` age-argmax with an O(1) per-set FIFO victim pointer.** `rr_set[NSET]` (WAYW bits/
   set) advanced on each rr-victim issue ≈ FIFO-per-set (rr naturally fills empty ways 0..WAY-1 first,
   then evicts oldest). Must still skip reserved (in-flight) ways to avoid double-victim. Removes the
   CARRY4×7 (the 16-bit fseq−seq subtracts) AND frees the 8192-FF `seq[512]×16b` array. Re-verify BOTH
   gates — it changes the eviction policy from global-FIFO to per-set-RR (should be equivalent for the
   streaming prefetch order, but prove it: underruns=0, bit-err=0, real-time).
2. **Then PIPELINE the suffix** (32 levels, 78% route, won't close by logic-trim alone — need ~10
   levels/stage). Split into ~3 stages with the agent's rule: keep the **`rsv` reservation combinational/
   immediate at issue** (victim now O(1) so the slot is known same-cycle the set is) and pipeline only
   the availability read behind a **k≈4 recently-issued shift-register checked combinationally** (a
   k-entry CAM) to cover the read-side shadow (cycles where a just-issued tile isn't yet in the arrays).
   This is the re-issue/double-victim hazard junction — re-verify both gates after.
3. Then check the consumer gather path (looka→baddr→BRAM, separate/shorter). Rebuild, read WNS.

Progress so far is monotone and sim-clean; the finish is careful hazard work. WHS healthy (+0.03).

### Fit round 5 (per-set RR victim): WNS −20.27 → −15.38, root cause = dynamic-addressed array reads
Per-set FIFO victim pointer (commit `<per-set-rr>`) removed the age-argmax: WNS −20.27 → **−15.38**,
CARRY4 11→2. Sim-verified (small TB 4/4; real-geom shrink/aniso/rot20 real-time). New worst path:
`u_tc/ps00_reg → u_tc/rr_set_reg`, **31 levels (LUT6=15, MUXF7=8, MUXF8=4, CARRY4=2), 76% route.**

**Root cause of the residue:** the tag/vld/rsv arrays are read at the COMPUTED slot `{ps, way}` — a
512-entry (NTILE) mux each (the MUXF7/8 cascade). The prefetch availability does 16 such reads
(4 tiles × WAY) and `vict` does WAY more; the chain `ps → array-read mux → compare → ua → vict →
ua_slot → tag/rsv/rr write` is the cone. Logic-trimming is exhausted (CARRY4 already gone); it must be
PIPELINED, and the array-read muxes are the deep part.

**Remaining closure (next session — multi-stage, careful):**
1. **Quick win first:** narrow `TIDW` 24→16 (tidf only uses {py[11:4],px[11:4]} = 16 b). Shrinks every
   tag mux + compare ~33% and the tag array. Low risk; re-verify gates.
2. **avm-snapshot (hazard-free) — the main lever.** Read each coord's 4-tile availability ONCE at
   coord-load (the deep array-read mux, pipelined into a registered 4-bit `avm` mask), then run the
   issue loop off `avm` + a local "issued" mask (set as tiles are reserved). This removes the array
   reads from the per-cycle issue loop entirely. It's hazard-free: coords process serially, so the
   snapshot + local updates are exact (no other coord issues mid-processing; prior issues are committed
   before s2_adv). Needs a 3rd prefetch stage (coord → ps/pt → avm+issue) with its own valid bit.
3. **Pipeline `vict`'s array reads** if it's then critical (it reads vld/rsv[{ua_set,way}] for the
   free-way scan): register the free-way/rr decision, or maintain a per-set "has-free-way" + the rr
   pointer incrementally so vict is a pure register read.
4. Rebuild; if still short, register the tag/vld/rsv READ itself (1-cycle) with the 1-entry
   current-issue bypass (issues commit to arrays in 1 cycle, so a 1-deep bypass covers the shadow).
Then check consumer gather; read WNS.

Progress this session: WNS −28.76 → −20.27 (feedforward pipeline) → −15.38 (per-set RR), monotone, each
step committed + both sim gates green. The finish is multi-stage prefetch pipelining (the array-read
muxes) — careful, re-verify-heavy, recommended fresh. WHS healthy throughout (+0.02).

### avm-snapshot design subtlety (resolved on paper — the key note for the fresh session)
Working the avm-snapshot through, the naive version DOESN'T work, for a non-obvious reason — document
this so it isn't re-discovered the hard way:
- **Compute avm combinationally each cycle** → the deep array-read mux is back on the path (the thing
  we're removing). No good.
- **Compute avm once at coord-LOAD into stage C** → 1-cycle bubble per coord. Fatal: hit-coords then
  take 2 cycles → prefetch advances ~0.5 coord/cycle < the consumer's ~0.78 (active fraction) → the lead
  erodes → starvation. (Verified by reasoning, not yet sim.)
- **Precompute avm one stage early (stage B, while stage C processes the current coord)** → STALE:
  adjacent coords SHARE tiles, so a tile coord-C reserves between the snapshot (T_b) and when coord-D
  is processed (T_c) is missed by avm(D) → D re-issues it → double-issue / wasted fetch / starvation.

**Resolution = the CAM bypass after all:** precompute avm in stage B, but OR-in a k-deep "recently
issued" list (the ua_tids issued since the snapshot) when loading stage C — `avm(D) =
precomputed_avail(D) | (D-tile ∈ recently_issued)`. k covers the issues in the snapshot→process window
(the current coord's ≤WAY issues + a margin; k≈WAY+2). This is the hazard junction the agent flagged;
it must be sim-verified (both gates) with attention to the shared-tile case (adjacent coords, and the
2×2 neighbour overlap within a coord). So the honest path is: **avm-snapshot (stage B precompute) +
k-deep recently-issued CAM bypass**, then pipeline vict, then re-time. Not a quick step — a careful
stateful pipeline with a real correctness hazard (double-issue via stale availability).

### ★ LEAD next-session step (CONFIRMED): the 512:1 mux is a STORAGE-SHAPE artifact, not inherent
Confirmed against source: `tag`/`vld`/`rsv` are declared `reg [..] x[0:NTILE-1]` (flat, 512 entries) and
read everywhere at the full slot `{set,way}` (e.g. `tag[{ps00,aw}]`, `vld[{st,w}]`) → a 9-bit dynamic
address → the 512:1 mux that IS the −15 ns critical cone (in both availability and vict). A set-assoc
cache should NOT produce this: the set should address storage, the ways come out in parallel as one wide
word, then W comparators.

**Try this FIRST next session — it may close timing with NO pipelining and NO re-issue hazard:**
- Restructure to set-indexed wide words: `reg [WAY*TIDW-1:0] tagset[0:NSET-1]` (+ `vldset`/`rsvset` =
  `reg [WAY-1:0] x[0:NSET-1]`). Read `tagset[set]` (a 128-deep addressed read → LUTRAM/shallow), split to
  WAY ways, do WAY parallel 24-bit comparators. The 512:1 mux → 128-deep read + WAY-way compare.
- The 2×2 needs 4 neighbour tiles in 4 different sets in ONE cycle = 4 simultaneous set-reads. Store
  `tagset` (etc.) as **LUTRAM replicated ×4** (128×96b ×4 ≈ 48 Kb distributed RAM — cheap on the 7020,
  async read = combinational, no added latency). 4 addresses → 4 wide words → the comparators. vict's
  free-way/rr reads the same wide word → benefits too.
- Writes: issue/fill write one way's slice — `tagset[set][way*TIDW +: TIDW] <= ...` (and the ×4 replicas).
- This is a STORAGE-SHAPE change, identical logic → re-verify is just the two gates (bit-exact). No new
  control flow, no double-issue hazard, no multi-stage re-verify.

Order: (1) this storage restructure → re-synth, read WNS. (2) If it closes → DONE (no pipelining, no
hazard). (3) If only partial → THEN the avm-snapshot+CAM pipelining on the residual, then vict. The
storage fix is the smaller, safer, fresh-head-friendly lever — lead with it.

### ★ Storage-shape fix BUILT (2026-06-08): WNS@74.25 -15.38 -> -4.69; SCOPE re-targeted to 1080p/148.5
Step-1 storage restructure (flat tag/vld/rsv[0:NTILE-1] -> set-indexed wide words tagset[0:NSET-1] +
vldset/rsvset, ways-in-parallel + W comparators; TIDW 24->16). Committed `ec95a04`. Both sim gates
green (small TB bit-exact 4/4; 720p real-geom rot20/shrink/aniso clean at per-geom leads, rot45 the
documented benign cold-start). Build `build_logs/warp_build_storageshape.log` (720p, WARP_ENGINE=1
NO_ILA=1):
- **WNS@74.25 (13.468 ns) = -4.691** (was -15.380) -> +10.69 ns, critical-path 28.85 -> 18.16 ns (-37%).
- Routed path: `tagset` now maps to **RAMD64E (LUTRAM)** + a single MUXF7 (old MUXF7=8/MUXF8=4 512:1
  cascade gone). Worst path is still the warp issue cone in `u_tc` (the number IS the warp logic).

**SCOPE CHANGE (Justin 2026-06-08, commit 019f47c):** warp must support **1080p OUTPUT** = 148.5 MHz /
6.734 ns. Re-targeted measurement (routed dcp, pclk retimed to 6.734 via `tcl/warp_timing_148.tcl`;
single-cycle pclk->pclk so slack drops 1:1 with period):
- **WNS@148.5 (6.734 ns) = -11.42** (measured) = -11.425 (arithmetic, WNS@74.25 - 6.734). Path 18.16 ns
  must reach 6.734 ns = 2.7x reduction.

The remaining 18.16 ns cone = the stateful issue loop, all combinational/cycle: `ps00_reg -> tagset
LUTRAM read + compare (av001) -> first-unavail -> victim (pf_slot) -> rsvset/tagset write` (~20 levels:
~7 ns tag-read front-end + ~11 ns victim/FIFO-slot LUT+CARRY4 cascade). This is exactly the Step-2
target (avm-snapshot removes the read from the loop; vict pipeline splits the cascade).

**1080p-out real-time RE-VALIDATION (sim, `sim/pg_warp_real_1080_tb.v`, 1920x1080<-1920x1080, 1:1-scale
rotation):** the 8-way/1024 cache + leads TRANSFER to 1080 out.
| LEAD  | rot20 | rot45 | rot10 | aniso |  (PASS = 2073600/2073600, 0 underrun, 0 bit-err)
| 1280  | PASS  | FAIL  | PASS  | PASS  |
| 32768 | PASS  | PASS  | PASS  | PASS  |  <- uniform lead clears all four at 1080 out
| 65536 | FAIL  | PASS  | PASS  | PASS  |
rot20 wants shallow / rot45 wants deep -> per-geometry LEAD (Step 3) widens margin but a uniform 32768
already clears this set at 1080 out. So 1080p real-time is NOT the blocker; TIMING is.

**THE FORK (grounded):**
1. **Step 2 (avm-snapshot + CAM + vict pipeline) is mandatory for ANY target** — even 720p@74.25 isn't
   closed (-4.69). Do it next; re-measure WNS@148.5 after.
2. **148.5/1px-clk reachability hinges on the issue-loop recurrence** (rsv-write must be visible to the
   next cycle's availability check or you double-issue — a true cycle pipelining can't break). If Step 2
   floors it < 6.734 -> single-clock 1080p ships. If not -> **2 px/clk @ 74.25** (13.468 ns budget; we're
   only -4.69 from closing there, so comfortable margin). De-risked fallback, not yet needed.

### Step 2 (avm-snapshot) BUILT 2026-06-08 — prefetch SOLVED; bottleneck moved to consumer gather + CDC
3-stage avm-snapshot (commit `bf9f0fd`, build `build_logs/warp_build_avmsnapshot.log`). Both gates green,
NO new underruns vs baseline (small TB bit-exact; 720p per-geom rot20/shrink/aniso clean + rot45 1
cold-start; 1080p all-four @32768 = 2073600/2073600). Freshness proof held (no double-issue).

**WNS journey (warp logic):** -15.38 (prefetch cone 28.85ns) -> storage fix -4.69 (cone 18.16) ->
avm-snapshot: the prefetch issue cone DROPS OUT of the top paths (SOLVED). New landscape:
- **Overall WNS@74.25 = -3.601** but this is the **GPIO->engine coefficient CDC** (`axi_gpio_8/
  gpio2_Data_Out -> pg_re_0/b1_reg`, src clk_fpga_0 100MHz -> dst pclk; data delay only 1.668ns, slack
  negative purely from the unconstrained async crossing). Same artifact as the color_correct -3.5ns note.
  **Fix = false-path / set_max_delay -datapath_only** in the XDC. Frame-atomic coeffs; functionally fine.
- **Real intra-pclk warp WNS = -1.868 @74.25 / -8.599 @148.5.** Worst path = the CONSUMER GATHER:
  `cx_/cy_ -> tidf -> tagset lookup (looka hit) -> stage_ready -> c_ready -> cx_/cy_ advance`, 18 levels,
  ~15.3ns. The looka hit-detection is combinational in the per-cycle consumer-advance decision — the SAME
  tag-lookup-in-the-loop shape the prefetch had, now the read-side limiter. Has a stall-on-miss recurrence.

**Refined fork (well-grounded now):**
- **720p single-px @74.25 is within reach:** (1) false-path the GPIO coeff CDC (removes -3.60), (2) close
  the consumer gather -1.868 (pipeline the looka hit-detect or logic-trim). Ships 720p warp.
- **1080p @148.5 single-clock:** consumer gather 15.3ns -> 6.734 (2.3x, stall hazard) PLUS re-pipeline
  prefetch to 6.734. Hard + uncertain.
- **2 px/clk @74.25 (RECOMMENDED for 1080p):** only needs <=13.468ns — we're at -1.868 (consumer) + the
  easy CDC false-path. Costs 2x cache read bandwidth (more banks / dual-port). Pragmatic 1080p path.
  Analysis tooling: `tcl/warp_timing_148.tcl` (overall), `tcl/warp_timing_148b.tcl` (intra-pclk isolation).

### 2026-06-08 cont'd — CDC false-path + consumer replica: WNS -3.60 -> -1.26 -> -0.93 (720p 94% closed)
After avm-snapshot, the limiter was (a) the GPIO coeff async CDC and (b) the consumer gather.
- **CDC false-path** (commit `a277861`): pg_warp_top already had the 2-FF ASYNC_REG sync (a1..f1/mt1 =
  q1); added the missing `set_false_path -to */a1_reg..f1_reg/mt1_reg/D` (scoped *pg_re_0*, verified 32/24
  pins). WNS -3.601 -> **-1.263** (router freed from the false path improved the real cone too).
- **Consumer tag+vld replica** (commit `c12fca3`): looka reads only vld+tag -> a consumer-private
  tagset_c/vldset_c written in parallel (identical contents, separate LUTRAM). Both gates match baseline.
  WNS -1.263 -> **-0.930**. Helped less than hoped: congestion placed tagset_c at X94 vs consumer X65
  (still 66% route), and the `setf` ×13/×7 multiply (CARRY4) is still IN the looka loop.
- Worst path now: `cx_ -> setf mult (CARRY4) -> tagset_c read (far route) -> compare -> stage_ready ->
  cx_ advance`, 14.07 ns (logic 4.78 / route 9.30), 16 levels. WNS@148.5 ~ -7.7.

**Next (foundational for BOTH 720p-single-px AND 2px/clk):** pipeline the consumer `setf`/`tidf` one stage
early — precompute the 2x2 neighbour set-indices+tile-ids from the INCOMING c_x/c_y and register them
alongside cx_/cy_ (the prefetch stage-1 feedforward trick, on the read side). Removes the multiply from
the looka loop; leaves looka = registered-read + compare. Delicate: the consumer gather has op_rdy
lockstep + stall-on-miss; the set-index precompute is feedforward (coord-only -> hazard-free) but the
restructure touches the 2-stage consumer control. Then the consumer needs the same avm-style read-pipeline
to reach 6.734 for single-clock 148.5 — which is exactly what the 2px/clk consumer rebuild subsumes.
