ibkickinit/schindler-clone/docs/warp-engine-briefing.md

# Warp read-engine — design briefing for external review

**Date:** 2026-06-07  **Status:** full HDL stack sim-verified; first in-context Vivado build running.
**Ask:** sanity-check the architecture and the silicon-closure decisions; flag anything wrong or risky
before this goes to the bench. Specific questions at the end.

---

## 1. Context

Schindler is an FPGA video frame-rate-converter / genlock box (Zynq-7020, Zybo Z7-20 dev board;
production target Trenz TE0720) for filming CRTs at film cadences. The existing **route-B read engine**
(`pg_read_engine_top`: `pg_addrgen` DDA + `pg_linefetch` line-ring + `pg_compose`) does scale / shift /
flip / 180° — anything whose source access is **row-monotonic**, because it caches whole source *lines*.

The **warp engine** is a new read path that does **arbitrary geometry** — rotation (any angle),
keystone, pincushion, mesh warp — by replacing the line-ring with a **tile cache**, so non-monotonic
2-D source access works. Output 1280×720, source 1920×1080, 60 Hz, pixel clock 74.25 MHz.

A behavioral feasibility gate (`tools/affine_tilecache_gate.py`, `tools/tilecache_realtime_gate.py`)
established the design point before any HDL: **16×16 tiles, ~256–512-tile BRAM cache, prefetch run-ahead
warmed during V-blank, single DDR port** → tear-free for all transforms. The HDL implements that.

## 2. Datapath architecture

```
   VTC sof ─┐
            ├─ pg_affine (consumer) ─┐
            └─ pg_affine (prefetch) ─┤
                                     ▼
   DDR ─ DataMover ─ pg_tile_dma ─► pg_tilecache_rt2 ─► bilinear ─► AXIS out ─► color stack ─ HDMI
        (64b beats)  (gearbox+        (4-bank, 4-way      (2-stage
                      2×2 reorder)     set-assoc, BRAM)     H/V lerp)
```

- **`pg_affine`** (`hdl/pg_affine.v`) — incremental 2×3 affine DDA, no per-pixel multiply. Emits, per
  *output* pixel, the inverse-mapped *source* coord `sx=a·ox+b·oy+c, sy=d·ox+e·oy+f` plus the
  sub-pixel fraction. Coeffs signed Q20.12, firmware-computed. Proper ready/valid producer (it advances
  only on accept — a pulse-valid version dropped coords when the cache stalled). Two instances: a
  **consumer** that feeds the gather and a **prefetch** that runs ahead (bounded) to warm the cache.

- **`pg_tilecache_rt2`** (`hdl/pg_tilecache_rt2.v`) — the hard module. Two concurrent engines share a
  4-bank tile BRAM + tag store:
  - **Gather (consumer):** 1 pixel/clock. The bilinear 2×2 can straddle up to 4 tiles; **4 parity
    banks** (bank = `{col&1,row&1}`) let all 4 neighbours be read in one cycle. Registered (synchronous)
    BRAM reads; a 2-stage pipeline carries the pixel's parity/edge/fraction alongside the read.
  - **Prefetch (fill):** walks the prefetch affine's coord stream ahead of the consumer, parallel 4-tile
    residency check, issues a single-in-flight DMA fill for misses. Lead is bounded so the round-robin
    victim only ever evicts a *consumed* tile.
  - **Tags: 4-way set-associative** (set = low bits of `{ty,tx}` so the 2×2's four tiles spread across
    sets; per-set round-robin victim). NTILE=256 (64 sets × 4 ways).
  - **Fill:** one **2×2 block per beat → all 4 banks written in parallel** at the same within-tile addr
    (`block = (row>>1)·8 + (col>>1)`).

- **`pg_tile_dma`** (`hdl/pg_tile_dma.v`) — bridges cache↔DataMover. On a cache `fetch_req(tx,ty)` it
  issues 16 row-fetches (`addr = base + (ty·16+r)·stride + tx·16·3`, BTT=48B), **gearboxes the 64-bit
  beats to 2 px/clock** (a 1px/clock unpack starved the cache), buffers the even row, pairs it with the
  odd row → 64 2×2-block fills.

- **bilinear** (in `hdl/pg_warp_engine.v`) — pipelined H row-lerps then V column-lerp; weight = top 8
  bits of the Q0.12 fraction.

- **`pg_warp_top`** (`hdl/pg_warp_top.v`) — BD wrapper, drop-in for `pg_read_engine_top`: same
  DataMover / frame_ptr / VTC / output-AXIS interface. Adds the DataMover cmd formatter, frame-base
  selection (latest completed VDMA slot, `frame_ptr-1`, latched at `sof = vsync rising`), coeff CDC, and
  output **TUSER=SOF / TLAST=EOL** framing for the downstream SOF-realign in `axis_to_vid_io`.
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
