ibkickinit/schindler-clone/Images/2026-05-21_iter1_input1_static_offset.jpg

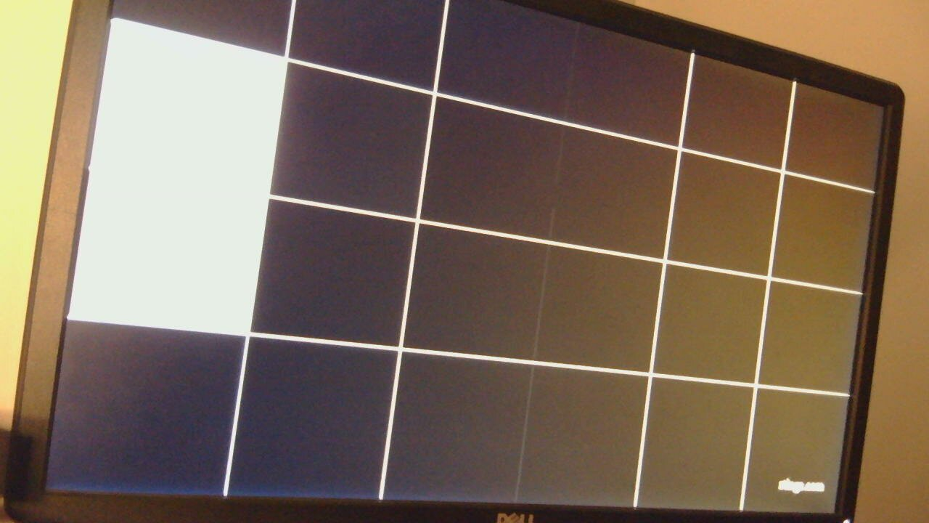
Images/2026-05-21_iter1_input1_static_offset.jpg
