ibkickinit/schindler-clone/Images/2026-05-21_iter1_input3_laptop.jpg

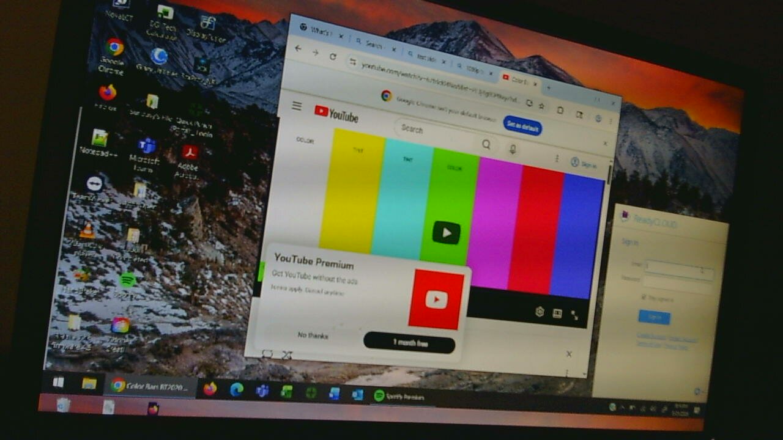
Images/2026-05-21_iter1_input3_laptop.jpg
