ibkickinit/schindler-clone/Images/2026-05-21_iter1_scaler_top_frame030.jpg

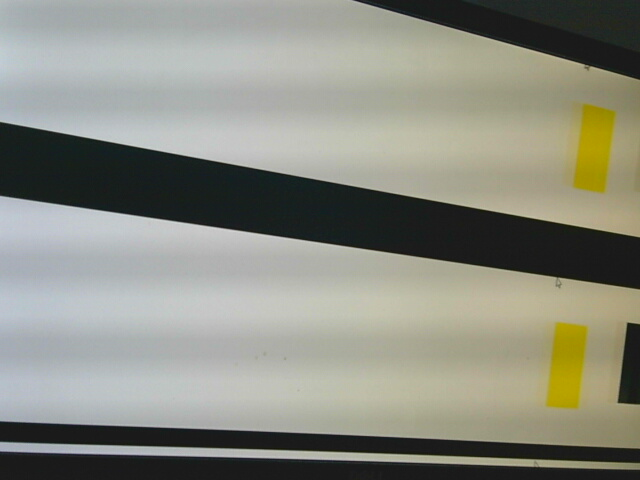
Images/2026-05-21_iter1_scaler_top_frame030.jpg
