ibkickinit/schindler-clone/Images/2026-05-21_iter4h_t0.0s.jpg

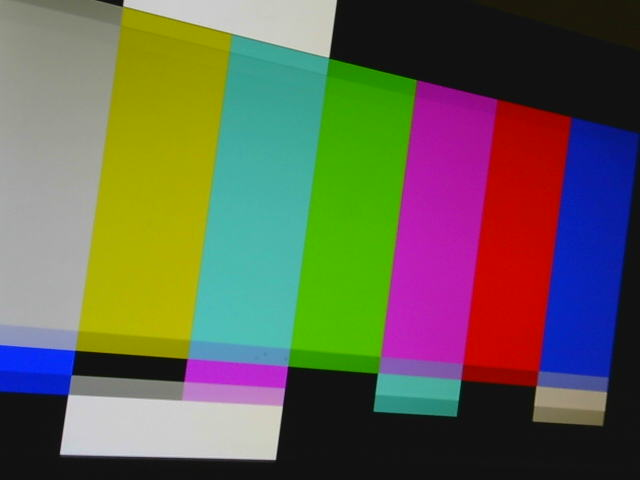
Images/2026-05-21_iter4h_t0.0s.jpg
