ibkickinit/schindler-clone/Images/2026-05-21_iter4h_t5.0s.jpg

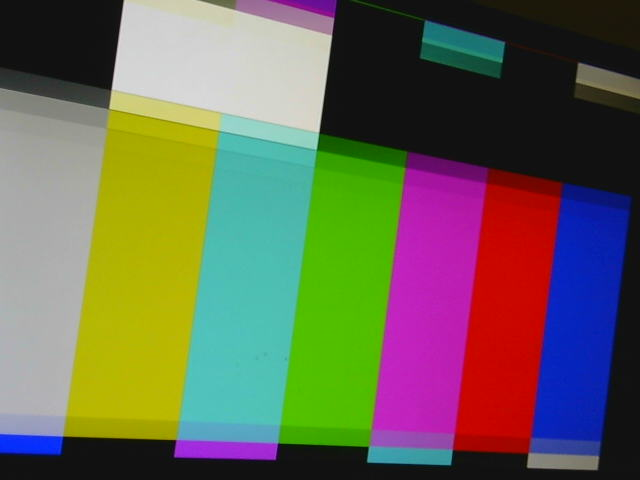
Images/2026-05-21_iter4h_t5.0s.jpg
