ibkickinit/schindler-clone/Images/2026-05-21_phaseA_clean_reference.jpg

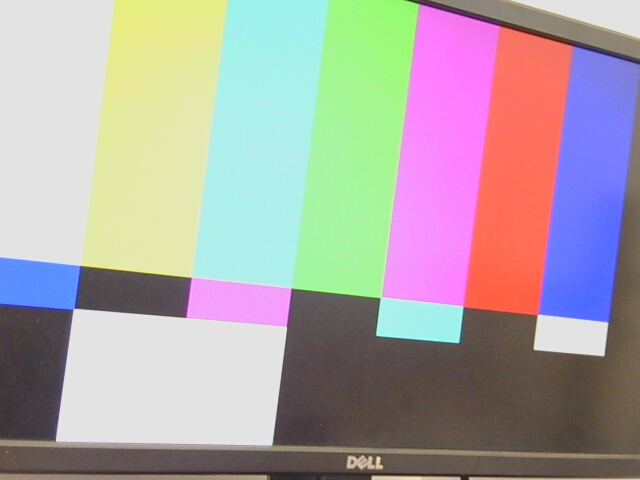
Images/2026-05-21_phaseA_clean_reference.jpg
