ibkickinit/schindler-clone/Images/2026-05-21_phaseA_input1_clean.jpg

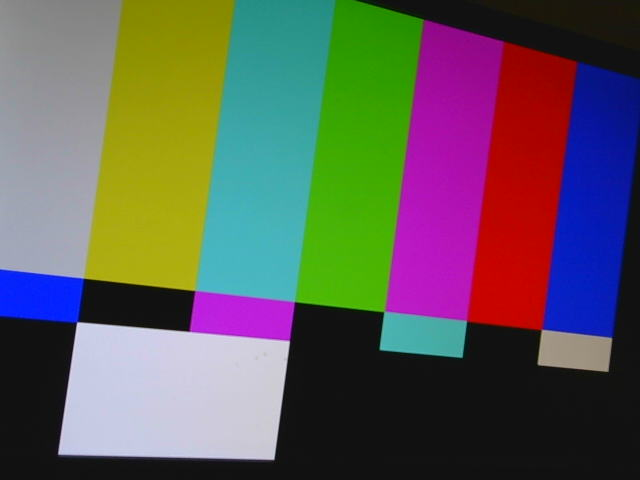
Images/2026-05-21_phaseA_input1_clean.jpg
