ibkickinit/schindler-clone/MVPHD24/DOCgzSFHVnvwromv3NfO_1758750654685.jpg

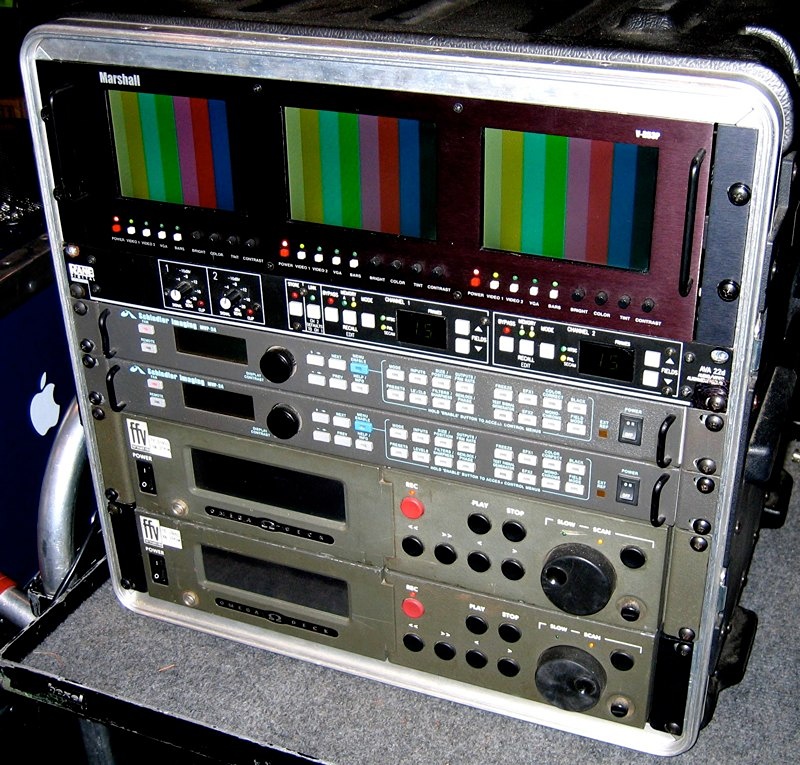
MVPHD24/DOCgzSFHVnvwromv3NfO_1758750654685.jpg
