ibkickinit/schindler-clone/MVPHD24/Front panel.jpeg

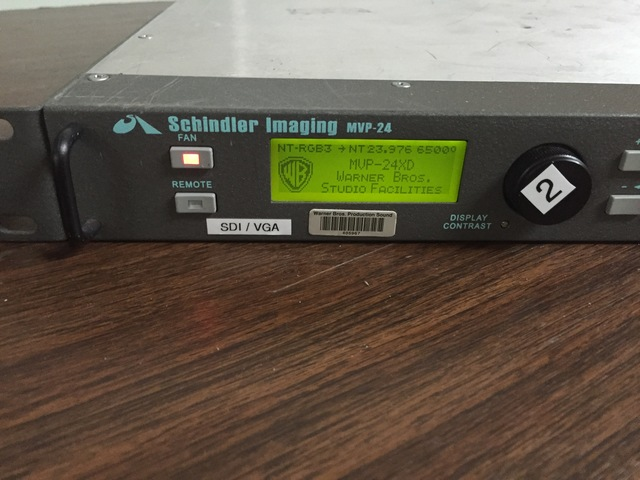
MVPHD24/Front panel.jpeg
