ibkickinit/schindler-clone/MVPHD24/MVPHD-24-on-white-table-top-only.jpg

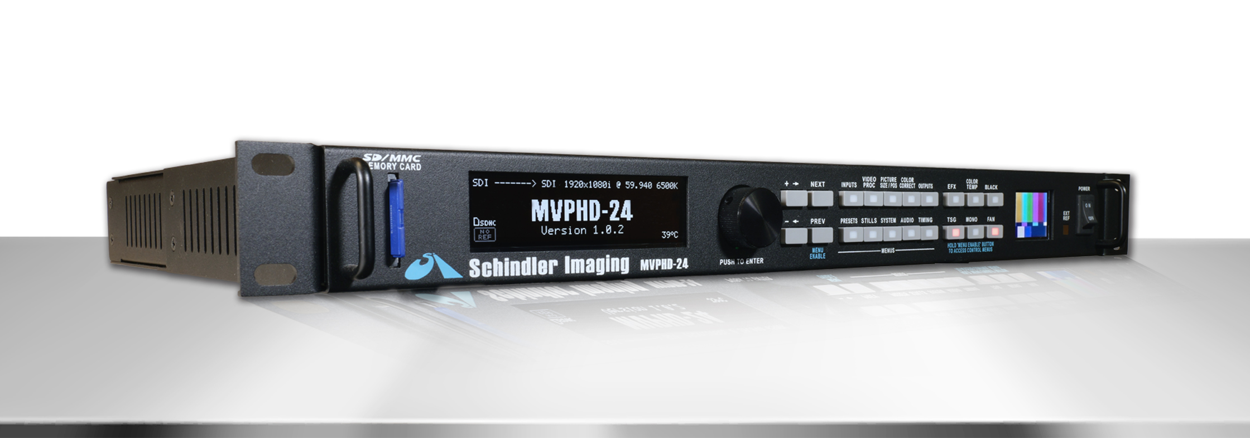
MVPHD24/MVPHD-24-on-white-table-top-only.jpg
