ibkickinit/schindler-clone/KiCad/SchindlerRFBoard_V1/SchindlerRFBoard_V1.kicad_pcb

## KiCad design KiCad/SchindlerRFBoard_V1/SchindlerRFBoard_V1.kicad_pcb (2026-06-09)

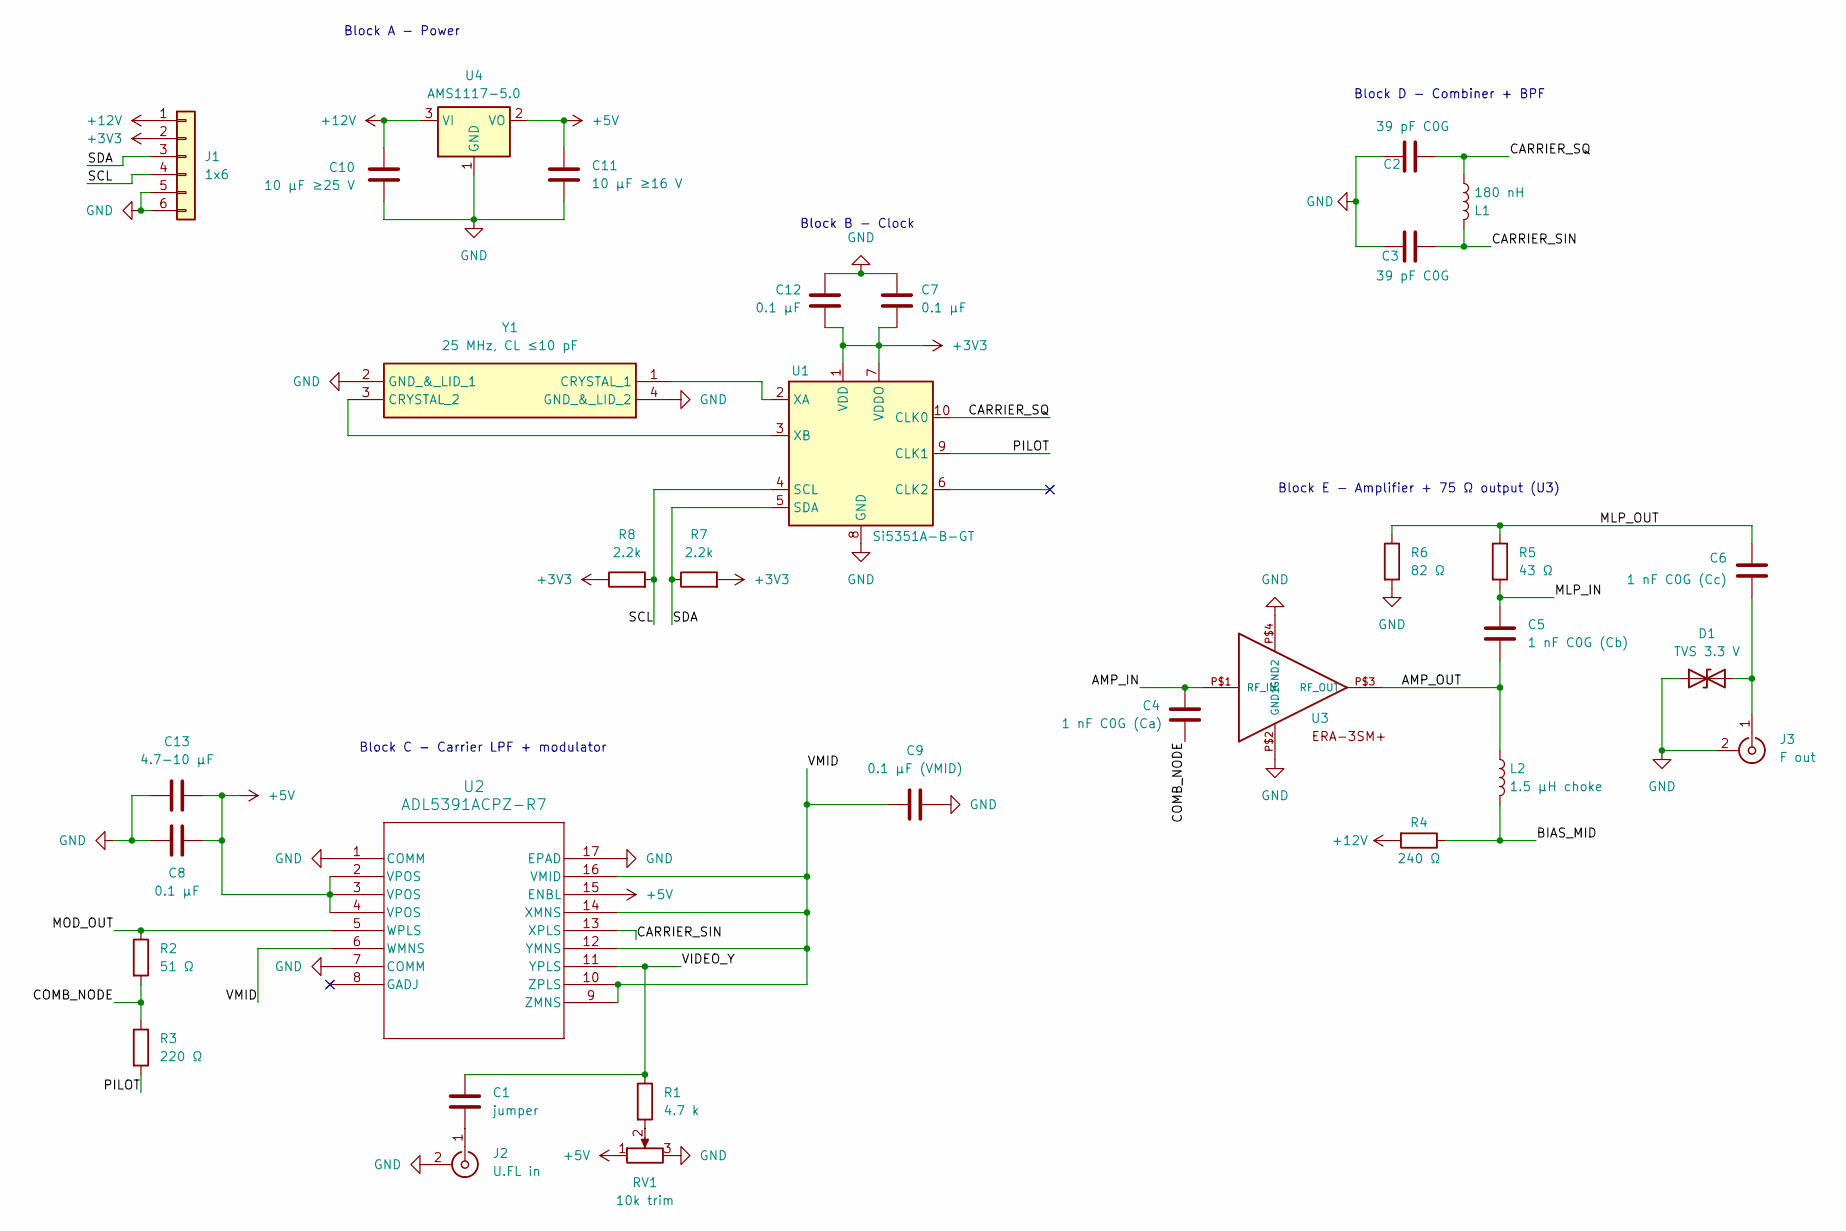
[picture p20: schematic SchindlerRFBoard_V1.kicad_sch]

Parts:
C1: jumper; C_0805_2012Metric
C2, C3: 39 pF C0G; C_0805_2012Metric
C4: 1 nF C0G (Ca); C_0805_2012Metric
C5: 1 nF C0G (Cb); C_0805_2012Metric
C6: 1 nF C0G (Cc); C_0805_2012Metric
C7, C8, C12: 0.1 µF; C_0805_2012Metric
C9: 0.1 µF (VMID); C_0805_2012Metric
C10: 10 µF ≥25 V; C_0805_2012Metric
C11: 10 µF ≥16 V; C_0805_2012Metric
C13: 4.7-10 µF; C_0805_2012Metric
D1: TVS 3.3 V; D_SOD-323
J1: 1x6; PinHeader_1x06_P1.00mm_Vertical
J2: U.FL in; U.FL_Hirose_U.FL-R-SMT-1_Vertical
J3: F out; U.FL_Hirose_U.FL-R-SMT-1_Vertical
L1: 180 nH; L_0805_2012Metric
L2: 1.5 µH choke; L_0805_2012Metric
R1: 4.7 k; R_0805_2012Metric
R2: 51 Ω; R_0805_2012Metric
R3: 220 Ω; R_0805_2012Metric
R4: 240 Ω; R_0805_2012Metric
R5: 43 Ω; R_0805_2012Metric
R6: 82 Ω; R_0805_2012Metric
R7, R8: 2.2k; R_0805_2012Metric
RV1: 10k trim; Potentiometer_Bourns_3296W_Vertical
U1: Si5351A-B-GT; MSOP-10_3x3mm_P0.5mm
U2: ADL5391ACPZ-R7; CP_16_27_ADI
U3: ERA-3SM+; WW107
U4: AMS1117-5.0; SOT-223-3_TabPin2
Y1: 25 MHz, CL ≤10 pF; LFXTAL072604; Manufacturer_Part_Number LFXTAL072604

Connections:
+3V3: C7.2, C12.2, J1.2, R7.2, R8.1, U1.1 (VDD), U1.7 (VDDO)
+5V: C8.1, C11.1, C13.1, RV1.1, U2.2 (VPOS), U2.3 (VPOS), U2.4 (VPOS), U2.15 (ENBL), U4.2 (VO)
+12V: C10.1, J1.1, R4.2, U4.3 (VI)
/AMP_IN: C4.2, U3.P$1 (RF_IN)
/AMP_OUT: C5.2, L2.1, U3.P$3 (RF_OUT)
/BIAS_MID: L2.2, R4.1
/CARRIER_SIN: C3.2, L1.2, U2.13 (XPLS)
/CARRIER_SQ: C2.1, L1.1, U1.10 (CLK0)
/COMB_NODE: C4.1, R2.2, R3.1
/MLP_IN: C5.1, R5.2
/MLP_OUT: C6.1, R5.1, R6.1
/MOD_OUT: R2.1, U2.5 (WPLS)
/PILOT: R3.2, U1.9 (CLK1)
/SCL: J1.4, R8.2, U1.4 (SCL)
/SDA: J1.3, R7.1, U1.5 (SDA)
/VIDEO_Y: C1.1, R1.1, U2.11 (YPLS)
/VMID: C9.1, U2.6 (WMNS), U2.9 (ZMNS), U2.10 (ZPLS), U2.12 (YMNS), U2.14 (XMNS), U2.16 (VMID)
GND: C2.2, C3.1, C7.1, C8.2, C9.2, C10.2, C11.2, C12.1, C13.2, D1.1 (A1), J1.5, J1.6, J2.2 (Ext), J3.2 (Ext), R6.2, RV1.3, U1.8 (GND), U2.1 (COMM), U2.7 (COMM), U2.17 (EPAD), U3.P$2 (GND1), U3.P$4 (GND2), U4.1 (GND), Y1.2 (GND_&_LID_1), Y1.4 (GND_&_LID_2)
unnamed: C6.2, D1.2 (A2), J3.1 (In)
unnamed: C1.2, J2.1 (In)
unnamed: R1.2, RV1.2
unnamed: U1.2 (XA), Y1.1 (CRYSTAL_1)
unnamed: U1.3 (XB), Y1.3 (CRYSTAL_2)

Notes on the sheet:
Block E - Amplifier + 75 Ω output (U3)
Block C - Carrier LPF + modulator
Block B - Clock
Block D - Combiner + BPF
Block A - Power

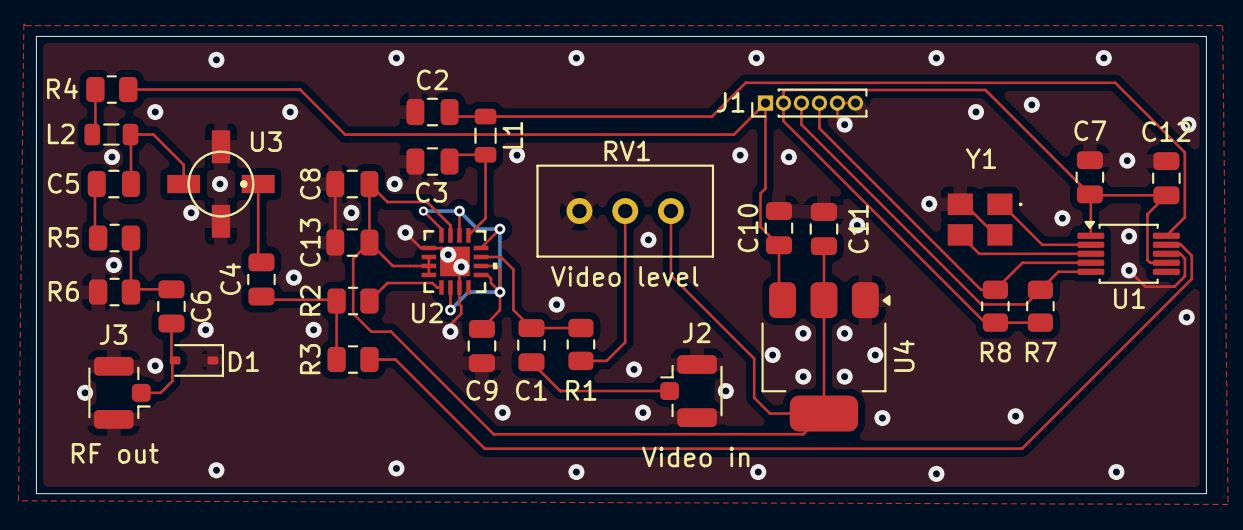
[picture p21: board SchindlerRFBoard_V1.kicad_pcb from above]

Board: 2 copper layers, 65.0 x 25.4 mm, 33 parts (0 on the bottom side), 23 nets.
