ibkickinit/schindler-clone/docs/schindler_plio.xdc

# Schindler 2.0 PL I/O constraints (seed) - TE0720 / xc7z020clg484
# Generated 2026-06-18 from pin-lock-substrate. Verify bus bit-order against final RTL.

set_property -dict { PACKAGE_PIN B19  IOSTANDARD LVCMOS33 } [get_ports { HDMIRX_PCLK }]; # JM1-61 B35_L13_P
set_property -dict { PACKAGE_PIN D20  IOSTANDARD LVCMOS33 } [get_ports { SYNC1_DAC_CLK }]; # JM1-67 B35_L14_P
set_property -dict { PACKAGE_PIN D18  IOSTANDARD LVCMOS33 } [get_ports { ADV7280_LLC }]; # JM1-77 B35_L12_P
set_property -dict { PACKAGE_PIN C22  IOSTANDARD LVCMOS33 } [get_ports { ADV7280_P0 }]; # JM1-31 B35_L16_N
set_property -dict { PACKAGE_PIN D22  IOSTANDARD LVCMOS33 } [get_ports { ADV7280_P1 }]; # JM1-33 B35_L16_P
set_property -dict { PACKAGE_PIN G22  IOSTANDARD LVCMOS33 } [get_ports { ADV7280_P2 }]; # JM1-35 B35_L24_N
set_property -dict { PACKAGE_PIN A19  IOSTANDARD LVCMOS33 } [get_ports { ADV7280_P3 }]; # JM1-36 B35_L10_N
set_property -dict { PACKAGE_PIN H22  IOSTANDARD LVCMOS33 } [get_ports { ADV7280_P4 }]; # JM1-37 B35_L24_P
set_property -dict { PACKAGE_PIN A18  IOSTANDARD LVCMOS33 } [get_ports { ADV7280_P5 }]; # JM1-38 B35_L10_P
set_property -dict { PACKAGE_PIN A17  IOSTANDARD LVCMOS33 } [get_ports { ADV7280_P6 }]; # JM1-40 B35_L9_N
set_property -dict { PACKAGE_PIN B22  IOSTANDARD LVCMOS33 } [get_ports { ADV7280_P7 }]; # JM1-41 B35_L18_N
set_property -dict { PACKAGE_PIN A16  IOSTANDARD LVCMOS33 } [get_ports { HDMIRX_D0 }]; # JM1-42 B35_L9_P
set_property -dict { PACKAGE_PIN B21  IOSTANDARD LVCMOS33 } [get_ports { HDMIRX_D1 }]; # JM1-43 B35_L18_P
set_property -dict { PACKAGE_PIN A22  IOSTANDARD LVCMOS33 } [get_ports { HDMIRX_D2 }]; # JM1-45 B35_L15_N
set_property -dict { PACKAGE_PIN B15  IOSTANDARD LVCMOS33 } [get_ports { HDMIRX_D3 }]; # JM1-46 B35_L7_N
set_property -dict { PACKAGE_PIN A21  IOSTANDARD LVCMOS33 } [get_ports { HDMIRX_D4 }]; # JM1-47 B35_L15_P
set_property -dict { PACKAGE_PIN C15  IOSTANDARD LVCMOS33 } [get_ports { HDMIRX_D5 }]; # JM1-48 B35_L7_P
set_property -dict { PACKAGE_PIN G21  IOSTANDARD LVCMOS33 } [get_ports { HDMIRX_D6 }]; # JM1-49 B35_L22_N
set_property -dict { PACKAGE_PIN D17  IOSTANDARD LVCMOS33 } [get_ports { HDMIRX_D7 }]; # JM1-50 B35_L2_N
set_property -dict { PACKAGE_PIN G20  IOSTANDARD LVCMOS33 } [get_ports { HDMIRX_D8 }]; # JM1-51 B35_L22_P
set_property -dict { PACKAGE_PIN D16  IOSTANDARD LVCMOS33 } [get_ports { HDMIRX_D9 }]; # JM1-52 B35_L2_P
set_property -dict { PACKAGE_PIN D21  IOSTANDARD LVCMOS33 } [get_ports { HDMIRX_D10 }]; # JM1-55 B35_L17_N
set_property -dict { PACKAGE_PIN B17  IOSTANDARD LVCMOS33 } [get_ports { HDMIRX_D11 }]; # JM1-56 B35_L8_N
set_property -dict { PACKAGE_PIN E21  IOSTANDARD LVCMOS33 } [get_ports { HDMIRX_D12 }]; # JM1-57 B35_L17_P
set_property -dict { PACKAGE_PIN B16  IOSTANDARD LVCMOS33 } [get_ports { HDMIRX_D13 }]; # JM1-58 B35_L8_P
set_property -dict { PACKAGE_PIN B20  IOSTANDARD LVCMOS33 } [get_ports { HDMIRX_D14 }]; # JM1-59 B35_L13_N
set_property -dict { PACKAGE_PIN E20  IOSTANDARD LVCMOS33 } [get_ports { HDMIRX_D15 }]; # JM1-60 B35_L21_N
set_property -dict { PACKAGE_PIN E19  IOSTANDARD LVCMOS33 } [get_ports { HDMIRX_DE }]; # JM1-62 B35_L21_P
set_property -dict { PACKAGE_PIN C20  IOSTANDARD LVCMOS33 } [get_ports { HDMIRX_HS }]; # JM1-65 B35_L14_N
set_property -dict { PACKAGE_PIN C18  IOSTANDARD LVCMOS33 } [get_ports { HDMIRX_VS }]; # JM1-66 B35_L11_N
set_property -dict { PACKAGE_PIN C17  IOSTANDARD LVCMOS33 } [get_ports { SYNC1_DAC_DB0 }]; # JM1-68 B35_L11_P
set_property -dict { PACKAGE_PIN G16  IOSTANDARD LVCMOS33 } [get_ports { SYNC1_DAC_DB1 }]; # JM1-69 B35_L4_N
set_property -dict { PACKAGE_PIN F22  IOSTANDARD LVCMOS33 } [get_ports { SYNC1_DAC_DB2 }]; # JM1-70 B35_L23_N
set_property -dict { PACKAGE_PIN G15  IOSTANDARD LVCMOS33 } [get_ports { SYNC1_DAC_DB3 }]; # JM1-71 B35_L4_P
set_property -dict { PACKAGE_PIN F21  IOSTANDARD LVCMOS33 } [get_ports { SYNC1_DAC_DB4 }]; # JM1-72 B35_L23_P
set_property -dict { PACKAGE_PIN C19  IOSTANDARD LVCMOS33 } [get_ports { SYNC1_DAC_DB5 }]; # JM1-75 B35_L12_N
set_property -dict { PACKAGE_PIN E18  IOSTANDARD LVCMOS33 } [get_ports { SYNC1_DAC_DB6 }]; # JM1-76 B35_L5_N
set_property -dict { PACKAGE_PIN F18  IOSTANDARD LVCMOS33 } [get_ports { SYNC1_DAC_DB7 }]; # JM1-78 B35_L5_P
set_property -dict { PACKAGE_PIN D15  IOSTANDARD LVCMOS33 } [get_ports { SYNC1_DAC_DB8 }]; # JM1-80 B35_L3_N
set_property -dict { PACKAGE_PIN F19  IOSTANDARD LVCMOS33 } [get_ports { SYNC1_DAC_DB9 }]; # JM1-81 B35_L20_N
set_property -dict { PACKAGE_PIN E15  IOSTANDARD LVCMOS33 } [get_ports { SYNC1_DAC_DB10 }]; # JM1-82 B35_L3_P
set_property -dict { PACKAGE_PIN G19  IOSTANDARD LVCMOS33 } [get_ports { SYNC1_DAC_DB11 }]; # JM1-83 B35_L20_P
set_property -dict { PACKAGE_PIN Y9  IOSTANDARD LVCMOS33 } [get_ports { HDMITX_PCLK }]; # JM2-46 B13_L12_P
set_property -dict { PACKAGE_PIN Y6  IOSTANDARD LVCMOS33 } [get_ports { VIDOUT_CLKIN }]; # JM2-56 B13_L13_P
set_property -dict { PACKAGE_PIN U12  IOSTANDARD LVCMOS33 } [get_ports { HDMITX_D0 }]; # JM2-32 B13_L5_P
set_property -dict { PACKAGE_PIN U11  IOSTANDARD LVCMOS33 } [get_ports { HDMITX_D1 }]; # JM2-34 B13_L5_N
set_property -dict { PACKAGE_PIN U10  IOSTANDARD LVCMOS33 } [get_ports { HDMITX_D2 }]; # JM2-36 B13_L6_P
set_property -dict { PACKAGE_PIN U9  IOSTANDARD LVCMOS33 } [get_ports { HDMITX_D3 }]; # JM2-38 B13_L6_N
set_property -dict { PACKAGE_PIN AA12  IOSTANDARD LVCMOS33 } [get_ports { HDMITX_D4 }]; # JM2-41 B13_L7_P
set_property -dict { PACKAGE_PIN V10  IOSTANDARD LVCMOS33 } [get_ports { HDMITX_D5 }]; # JM2-42 B13_L1_P
set_property -dict { PACKAGE_PIN AB12  IOSTANDARD LVCMOS33 } [get_ports { HDMITX_D6 }]; # JM2-43 B13_L7_N
set_property -dict { PACKAGE_PIN V9  IOSTANDARD LVCMOS33 } [get_ports { HDMITX_D7 }]; # JM2-44 B13_L1_N
set_property -dict { PACKAGE_PIN AA11  IOSTANDARD LVCMOS33 } [get_ports { HDMITX_D8 }]; # JM2-45 B13_L8_P
set_property -dict { PACKAGE_PIN AB11  IOSTANDARD LVCMOS33 } [get_ports { HDMITX_D9 }]; # JM2-47 B13_L8_N
set_property -dict { PACKAGE_PIN Y8  IOSTANDARD LVCMOS33 } [get_ports { HDMITX_D10 }]; # JM2-48 B13_L12_N
set_property -dict { PACKAGE_PIN AA9  IOSTANDARD LVCMOS33 } [get_ports { HDMITX_D11 }]; # JM2-51 B13_L11_P
set_property -dict { PACKAGE_PIN AA7  IOSTANDARD LVCMOS33 } [get_ports { HDMITX_D12 }]; # JM2-52 B13_L14_P
set_property -dict { PACKAGE_PIN AA8  IOSTANDARD LVCMOS33 } [get_ports { HDMITX_D13 }]; # JM2-53 B13_L11_N
set_property -dict { PACKAGE_PIN AA6  IOSTANDARD LVCMOS33 } [get_ports { HDMITX_D14 }]; # JM2-54 B13_L14_N
set_property -dict { PACKAGE_PIN AB10  IOSTANDARD LVCMOS33 } [get_ports { HDMITX_D15 }]; # JM2-55 B13_L9_P
set_property -dict { PACKAGE_PIN AB9  IOSTANDARD LVCMOS33 } [get_ports { HDMITX_DE }]; # JM2-57 B13_L9_N
set_property -dict { PACKAGE_PIN Y5  IOSTANDARD LVCMOS33 } [get_ports { HDMITX_HS }]; # JM2-58 B13_L13_N
set_property -dict { PACKAGE_PIN T4  IOSTANDARD LVCMOS33 } [get_ports { HDMITX_VS }]; # JM2-61 B13_L20_P
set_property -dict { PACKAGE_PIN V12  IOSTANDARD LVCMOS33 } [get_ports { VIDOUT_P0 }]; # JM2-62 B13_L4_P
set_property -dict { PACKAGE_PIN U4  IOSTANDARD LVCMOS33 } [get_ports { VIDOUT_P1 }]; # JM2-63 B13_L20_N
set_property -dict { PACKAGE_PIN W12  IOSTANDARD LVCMOS33 } [get_ports { VIDOUT_P2 }]; # JM2-64 B13_L4_N
set_property -dict { PACKAGE_PIN AB7  IOSTANDARD LVCMOS33 } [get_ports { VIDOUT_P3 }]; # JM2-65 B13_L17_P
set_property -dict { PACKAGE_PIN W11  IOSTANDARD LVCMOS33 } [get_ports { VIDOUT_P4 }]; # JM2-66 B13_L3_P
set_property -dict { PACKAGE_PIN AB6  IOSTANDARD LVCMOS33 } [get_ports { VIDOUT_P5 }]; # JM2-67 B13_L17_N
set_property -dict { PACKAGE_PIN W10  IOSTANDARD LVCMOS33 } [get_ports { VIDOUT_P6 }]; # JM2-68 B13_L3_N
set_property -dict { PACKAGE_PIN AB5  IOSTANDARD LVCMOS33 } [get_ports { VIDOUT_P7 }]; # JM2-71 B13_L16_P
set_property -dict { PACKAGE_PIN Y11  IOSTANDARD LVCMOS33 } [get_ports { VIDOUT_P8 }]; # JM2-72 B13_L10_P
set_property -dict { PACKAGE_PIN AB4  IOSTANDARD LVCMOS33 } [get_ports { VIDOUT_P9 }]; # JM2-73 B13_L16_N
set_property -dict { PACKAGE_PIN Y10  IOSTANDARD LVCMOS33 } [get_ports { VIDOUT_P10 }]; # JM2-74 B13_L10_N
set_property -dict { PACKAGE_PIN Y4  IOSTANDARD LVCMOS33 } [get_ports { VIDOUT_P11 }]; # JM2-75 B13_L18_P
set_property -dict { PACKAGE_PIN V8  IOSTANDARD LVCMOS33 } [get_ports { VIDOUT_P12 }]; # JM2-76 B13_L2_P
set_property -dict { PACKAGE_PIN AA4  IOSTANDARD LVCMOS33 } [get_ports { VIDOUT_P13 }]; # JM2-77 B13_L18_N
set_property -dict { PACKAGE_PIN W8  IOSTANDARD LVCMOS33 } [get_ports { VIDOUT_P14 }]; # JM2-78 B13_L2_N
set_property -dict { PACKAGE_PIN AB2  IOSTANDARD LVCMOS33 } [get_ports { VIDOUT_P15 }]; # JM2-81 B13_L15_P
set_property -dict { PACKAGE_PIN V7  IOSTANDARD LVCMOS33 } [get_ports { VIDOUT_HSYNC }]; # JM2-82 B13_L23_P
set_property -dict { PACKAGE_PIN AB1  IOSTANDARD LVCMOS33 } [get_ports { VIDOUT_VSYNC }]; # JM2-83 B13_L15_N
set_property -dict { PACKAGE_PIN W7  IOSTANDARD LVCMOS33 } [get_ports { VIDOUT_SFL }]; # JM2-84 B13_L23_N
set_property -dict { PACKAGE_PIN L18  IOSTANDARD LVCMOS18 } [get_ports { SDIRX_PCLK }]; # JM3-31 B34_L12_P
set_property -dict { PACKAGE_PIN M19  IOSTANDARD LVCMOS18 } [get_ports { SDITX_PCLK }]; # JM3-32 B34_L13_P
set_property -dict { PACKAGE_PIN J18  IOSTANDARD LVCMOS18 } [get_ports { SDIRX_D0 }]; # JM3-7 B34_L7_P
set_property -dict { PACKAGE_PIN J15  IOSTANDARD LVCMOS18 } [get_ports { SDIRX_D1 }]; # JM3-8 B34_L1_P
set_property -dict { PACKAGE_PIN K18  IOSTANDARD LVCMOS18 } [get_ports { SDIRX_D2 }]; # JM3-9 B34_L7_N
set_property -dict { PACKAGE_PIN K15  IOSTANDARD LVCMOS18 } [get_ports { SDIRX_D3 }]; # JM3-10 B34_L1_N
set_property -dict { PACKAGE_PIN J16  IOSTANDARD LVCMOS18 } [get_ports { SDIRX_D4 }]; # JM3-13 B34_L2_P
set_property -dict { PACKAGE_PIN P20  IOSTANDARD LVCMOS18 } [get_ports { SDIRX_D5 }]; # JM3-14 B34_L18_P
set_property -dict { PACKAGE_PIN J17  IOSTANDARD LVCMOS18 } [get_ports { SDIRX_D6 }]; # JM3-15 B34_L2_N
set_property -dict { PACKAGE_PIN P21  IOSTANDARD LVCMOS18 } [get_ports { SDIRX_D7 }]; # JM3-16 B34_L18_N
set_property -dict { PACKAGE_PIN L17  IOSTANDARD LVCMOS18 } [get_ports { SDIRX_D8 }]; # JM3-19 B34_L4_P
set_property -dict { PACKAGE_PIN P17  IOSTANDARD LVCMOS18 } [get_ports { SDIRX_D9 }]; # JM3-20 B34_L20_P
set_property -dict { PACKAGE_PIN M17  IOSTANDARD LVCMOS18 } [get_ports { SDITX_D0 }]; # JM3-21 B34_L4_N
set_property -dict { PACKAGE_PIN P18  IOSTANDARD LVCMOS18 } [get_ports { SDITX_D1 }]; # JM3-22 B34_L20_N
set_property -dict { PACKAGE_PIN N17  IOSTANDARD LVCMOS18 } [get_ports { SDITX_D2 }]; # JM3-25 B34_L5_P
set_property -dict { PACKAGE_PIN L21  IOSTANDARD LVCMOS18 } [get_ports { SDITX_D3 }]; # JM3-26 B34_L10_P
set_property -dict { PACKAGE_PIN N18  IOSTANDARD LVCMOS18 } [get_ports { SDITX_D4 }]; # JM3-27 B34_L5_N
set_property -dict { PACKAGE_PIN L22  IOSTANDARD LVCMOS18 } [get_ports { SDITX_D5 }]; # JM3-28 B34_L10_N
set_property -dict { PACKAGE_PIN L19  IOSTANDARD LVCMOS18 } [get_ports { SDITX_D6 }]; # JM3-33 B34_L12_N
set_property -dict { PACKAGE_PIN M20  IOSTANDARD LVCMOS18 } [get_ports { SDITX_D7 }]; # JM3-34 B34_L13_N
set_property -dict { PACKAGE_PIN J21  IOSTANDARD LVCMOS18 } [get_ports { SDITX_D8 }]; # JM3-37 B34_L8_P
set_property -dict { PACKAGE_PIN T16  IOSTANDARD LVCMOS18 } [get_ports { SDITX_D9 }]; # JM3-38 B34_L21_P
set_property -dict { PACKAGE_PIN Y18  IOSTANDARD LVCMOS18 } [get_ports { GENADC_DCO }]; # JM2-25 B33_L12_P
set_property -dict { PACKAGE_PIN AA22  IOSTANDARD LVCMOS18 } [get_ports { GENADC_D0 }]; # JM2-11 B33_L7_P
set_property -dict { PACKAGE_PIN AB22  IOSTANDARD LVCMOS18 } [get_ports { GENADC_D1 }]; # JM2-13 B33_L7_N
set_property -dict { PACKAGE_PIN W20  IOSTANDARD LVCMOS18 } [get_ports { GENADC_D2 }]; # JM2-14 B33_L4_P
set_property -dict { PACKAGE_PIN AA21  IOSTANDARD LVCMOS18 } [get_ports { GENADC_D3 }]; # JM2-15 B33_L8_P
set_property -dict { PACKAGE_PIN W21  IOSTANDARD LVCMOS18 } [get_ports { GENADC_D4 }]; # JM2-16 B33_L4_N
set_property -dict { PACKAGE_PIN AB21  IOSTANDARD LVCMOS18 } [get_ports { GENADC_D5 }]; # JM2-17 B33_L8_N
set_property -dict { PACKAGE_PIN Y19  IOSTANDARD LVCMOS18 } [get_ports { GENADC_D6 }]; # JM2-21 B33_L11_P
set_property -dict { PACKAGE_PIN W17  IOSTANDARD LVCMOS18 } [get_ports { GENADC_D7 }]; # JM2-22 B33_L13_P
set_property -dict { PACKAGE_PIN AA19  IOSTANDARD LVCMOS18 } [get_ports { GENADC_D8 }]; # JM2-23 B33_L11_N
set_property -dict { PACKAGE_PIN W18  IOSTANDARD LVCMOS18 } [get_ports { GENADC_D9 }]; # JM2-24 B33_L13_N
set_property -dict { PACKAGE_PIN W16  IOSTANDARD LVCMOS18 } [get_ports { SYNC2_BIPHASE }]; # JM2-26 B33_L14_P
