ibkickinit/schindler-clone/control-plane/schindlerd/schindlerd.py

#!/usr/bin/env python3
"""schindlerd — V0a host-side bridge daemon for Schindler 2.0 control plane.

Bridges:
  - Bare-metal firmware over /dev/ttyUSB1 (JSON-RPC via the 'J' UART command)
  - Web UI / future remote surfaces over WebSocket on :8080

Single-file v0.1 skeleton. Refactor into a package when it grows past ~600 LOC.

Dependencies: pyserial, websockets. Install:
    pip install pyserial websockets

Run:
    python schindlerd.py --port /dev/ttyUSB1 --catalog ../catalog-v0.2.0.json

Architecture: docs/control-plane-architecture.md §V0a.
"""

from __future__ import annotations

import argparse
import asyncio
import json
import logging
import os
import re
import sys
import threading
import time
from dataclasses import dataclass, field
from pathlib import Path
from typing import Any, Awaitable, Callable, Dict, List, Optional

try:
    import serial  # type: ignore
except ImportError:
    print("schindlerd: pyserial required (pip install pyserial)", file=sys.stderr)
    sys.exit(2)

try:
    import websockets  # type: ignore
    from websockets.server import WebSocketServerProtocol  # type: ignore
except ImportError:
    print("schindlerd: websockets required (pip install websockets)", file=sys.stderr)
    sys.exit(2)


log = logging.getLogger("schindlerd")


# ---------------------------------------------------------------------------
# Catalog
# ---------------------------------------------------------------------------

@dataclass
class CatalogControl:
    """One control from catalog.controls[]. Subset of the schema we need
    runtime; everything else is opaque pass-through to clients."""
    id: str
    type: str                       # "number" | "enum" | "boolean" | "trigger" | "text"
    raw: Dict[str, Any] = field(default_factory=dict)
    enum_str_to_int: Dict[str, int] = field(default_factory=dict)
    enum_int_to_str: Dict[int, str] = field(default_factory=dict)
    read_only: bool = False

    @classmethod
    def from_json(cls, j: Dict[str, Any]) -> "CatalogControl":
        c = cls(id=j["id"], type=j["type"], raw=j, read_only=bool(j.get("read_only")))
        if c.type == "enum":
            for idx, opt in enumerate(j.get("options", [])):
                v = opt["value"]
                c.enum_str_to_int[v] = idx
                c.enum_int_to_str[idx] = v
        return c

    def coerce_to_firmware(self, value: Any) -> int:
        """Translate client-side value (string for enums, number for everything
        else) into the integer the firmware J command expects."""
        if self.type == "enum":
            if isinstance(value, str):
                if value not in self.enum_str_to_int:
                    raise ValueError(f"unknown enum value '{value}' for {self.id}")
                return self.enum_str_to_int[value]
            if isinstance(value, int):
                if value not in self.enum_int_to_str:
                    raise ValueError(f"enum index {value} out of range for {self.id}")
                return value
            raise ValueError(f"{self.id}: enum value must be string or int")
        if self.type == "number":
            return int(value)
        if self.type == "boolean":
            return 1 if value else 0
        raise ValueError(f"{self.id}: type '{self.type}' is not settable via control.set")

    def coerce_from_firmware(self, value: int) -> Any:
        if self.type == "enum":
            return self.enum_int_to_str.get(value, value)
        if self.type == "boolean":
            return bool(value)
        return value


@dataclass
class Catalog:
    version: str
    controls: Dict[str, CatalogControl]
    raw: Dict[str, Any]
    available_ids: Optional[set] = None  # firmware-reported set; None = not probed yet

    @classmethod
    def load(cls, path: Path) -> "Catalog":
        raw = json.loads(path.read_text())
        controls = {}
        for c in raw.get("controls", []):
            controls[c["id"]] = CatalogControl.from_json(c)
        return cls(version=raw.get("schema_version", "0.0.0"), controls=controls, raw=raw)

    def annotated_raw(self) -> Dict[str, Any]:
        """Return the catalog with each control tagged 'available' based on
        what the firmware reported via system.list_controls. Status-type
        controls are always 'available' from the client's perspective (the
        daemon synthesizes them; firmware needn't know about them). Controls
        with requires_status == 'placeholder' are forced unavailable."""
        out = json.loads(json.dumps(self.raw))  # deep copy
        avail = self.available_ids or set()
        for c in out.get("controls", []):
            cid = c["id"]
            placeholder = c.get("requires_status") == "placeholder"
            if c.get("category") == "status" or c.get("read_only"):
                c["available"] = not placeholder
            else:
                c["available"] = (cid in avail) and not placeholder
        return out


# ---------------------------------------------------------------------------
# UART bridge — runs in a worker thread, talks to the firmware over /dev/ttyUSBn
# ---------------------------------------------------------------------------

class UartBridge:
    """Thread-safe UART bridge. send() submits a JSON-RPC request and returns
    a Future that resolves with the firmware's response. Concurrent requests
    are serialized via a per-instance request queue + per-request id."""

    JSON_LINE_RE = re.compile(rb"^\s*\{.*\}\s*$")

    def __init__(self, port: str, baud: int = 115200):
        self.port = port
        self.baud = baud
        self.ser: Optional[serial.Serial] = None
        self._next_id = 1
        self._pending: Dict[int, asyncio.Future] = {}
        self._lock = threading.Lock()
        self._loop: Optional[asyncio.AbstractEventLoop] = None
        self._stop = threading.Event()
        self._reader_thread: Optional[threading.Thread] = None
        # Non-JSON UART lines (firmware DIAG/TELEMETRY/etc) get routed to this
        # callback on the asyncio loop. Set externally by the daemon.
        self.text_log_handler: Optional[Callable[[str], None]] = None

    def start(self, loop: asyncio.AbstractEventLoop) -> None:
        self._loop = loop
        self.ser = serial.Serial(self.port, self.baud, timeout=0.1)
        self._reader_thread = threading.Thread(target=self._reader_loop, daemon=True)
        self._reader_thread.start()
        log.info("uart: opened %s @ %d", self.port, self.baud)

    def stop(self) -> None:
        self._stop.set()
        if self.ser:
            self.ser.close()

    def _reader_loop(self) -> None:
        assert self.ser is not None and self._loop is not None
        buf = bytearray()
        while not self._stop.is_set():
            try:
                chunk = self.ser.read(256)
            except Exception as e:
                log.warning("uart: read error: %s", e)
                time.sleep(0.5)
                continue
            if not chunk:
                continue
            buf.extend(chunk)
            while b"\n" in buf:
                line, _, rest = buf.partition(b"\n")
                buf = bytearray(rest)
                line = line.rstrip(b"\r")
                if not line:
                    continue
                if self.JSON_LINE_RE.match(line):
                    self._on_json_line(line)
                else:
                    text = line.decode("utf-8", "replace")
                    log.debug("uart-log: %s", text)
                    if self.text_log_handler and self._loop:
                        self._loop.call_soon_threadsafe(self.text_log_handler, text)

    def _on_json_line(self, line: bytes) -> None:
        try:
            obj = json.loads(line)
        except json.JSONDecodeError:
            log.warning("uart: malformed JSON: %s", line)
            return
        rid = obj.get("id")
        if not isinstance(rid, int):
            log.debug("uart: notification or null-id frame: %s", obj)
            return
        with self._lock:
            fut = self._pending.pop(rid, None)
        if fut is None:
            log.warning("uart: response for unknown id %d: %s", rid, obj)
            return
        assert self._loop is not None
        self._loop.call_soon_threadsafe(fut.set_result, obj)

    async def request(self, method: str, params: Optional[Dict[str, Any]] = None,
                       timeout: float = 1.5) -> Dict[str, Any]:
        assert self._loop is not None and self.ser is not None
        with self._lock:
            rid = self._next_id
            self._next_id += 1
        req = {"jsonrpc": "2.0", "id": rid, "method": method}
        if params is not None:
            req["params"] = params
        fut = self._loop.create_future()
        with self._lock:
            self._pending[rid] = fut
        line = "J " + json.dumps(req, separators=(",", ":")) + "\r\n"
        try:
            self.ser.write(line.encode("ascii"))
        except Exception as e:
            with self._lock:
                self._pending.pop(rid, None)
            raise RuntimeError(f"uart write failed: {e}") from e
        try:
            return await asyncio.wait_for(fut, timeout=timeout)
        except asyncio.TimeoutError:
            with self._lock:
                self._pending.pop(rid, None)
            raise

    def send_raw(self, line: str) -> None:
        """Send a RAW (non-JSON-RPC) firmware command line, fire-and-forget.
        For commands outside the catalog/JSON-RPC path — e.g. the read-engine
        geometry 'G w h x y'. The firmware echoes a non-JSON 'GEO:' line which the
        reader logs; there is no response correlation (so this returns nothing)."""
        if self.ser is None:
            raise RuntimeError("uart not open")
        try:
            self.ser.write((line.rstrip() + "\r\n").encode("ascii"))
        except Exception as e:
            raise RuntimeError(f"uart raw write failed: {e}") from e


# ---------------------------------------------------------------------------
# Profile store — JSON files in ~/.schindler/profiles/
# ---------------------------------------------------------------------------

class ProfileStore:
    """Multi-source profile store. The first root is the writable user dir;
    additional roots (e.g. factory presets shipped with the daemon) are
    read-only. Name collisions resolve to the first matching root, so a
    user profile shadows a factory profile of the same name."""

    def __init__(self, user_root: Path, readonly_roots: Optional[List[Path]] = None):
        self.user_root = user_root
        self.user_root.mkdir(parents=True, exist_ok=True)
        self.readonly_roots = [p for p in (readonly_roots or []) if p.is_dir()]

    def list(self) -> List[Dict[str, Any]]:
        """List visible profiles. Each entry: {name, factory: bool, source}."""
        seen: Dict[str, Dict[str, Any]] = {}
        for p in self.user_root.glob("*.json"):
            seen[p.stem] = {"name": p.stem, "factory": False, "source": "user"}
        for root in self.readonly_roots:
            for p in root.glob("*.json"):
                if p.stem in seen:
                    continue
                seen[p.stem] = {"name": p.stem, "factory": True, "source": root.name}
        return sorted(seen.values(), key=lambda r: (not r["factory"], r["name"]))

    def load(self, name: str) -> Dict[str, Any]:
        user_path = self.user_root / f"{name}.json"
        if user_path.is_file():
            return json.loads(user_path.read_text())
        for root in self.readonly_roots:
            p = root / f"{name}.json"
            if p.is_file():
                return json.loads(p.read_text())
        raise FileNotFoundError(f"no profile '{name}'")

    def save(self, name: str, profile: Dict[str, Any]) -> None:
        # Saving always writes to the user dir; never touches factory dirs.
        (self.user_root / f"{name}.json").write_text(json.dumps(profile, indent=2))


# ---------------------------------------------------------------------------
# Status cache + telemetry parser — converts firmware text lines into typed
# status fields broadcast as JSON-RPC notifications to all connected WS clients.
# ---------------------------------------------------------------------------

class Subscriber:
    """One bus subscriber: queue + per-client stats. Stats are exposed via
    system.metrics so an operator can see whether a client is keeping up."""
    __slots__ = ("q", "label", "published", "dropped", "consecutive_drops",
                 "last_drop_warned")

    def __init__(self, label: str, maxsize: int = 64):
        self.q: asyncio.Queue = asyncio.Queue(maxsize=maxsize)
        self.label = label
        self.published = 0
        self.dropped = 0
        self.consecutive_drops = 0
        self.last_drop_warned = 0


class StatusBus:
    """In-process pub-sub for status fields. Clients subscribe() and receive a
    Subscriber wrapping an asyncio.Queue. WS handler drains the queue and
    forwards as JSON-RPC notifications.

    Drops are tracked per-client. If a single client misses 10 events in a
    row we log a warning (probable backpressure or runaway client). Total
    counters survive across subscribers and feed system.metrics."""

    DROP_WARN_THRESHOLD = 10  # consecutive drops before logging

    def __init__(self):
        self._subs: List[Subscriber] = []
        self._lock = asyncio.Lock()
        self.total_published = 0
        self.total_dropped = 0
        self._next_id = 1

    async def subscribe(self, label: Optional[str] = None) -> Subscriber:
        async with self._lock:
            sub_id = self._next_id
            self._next_id += 1
        sub = Subscriber(label or f"client-{sub_id}")
        async with self._lock:
            self._subs.append(sub)
        return sub

    async def unsubscribe(self, sub: Subscriber) -> None:
        async with self._lock:
            if sub in self._subs:
                self._subs.remove(sub)

    def publish(self, payload: Dict[str, Any]) -> None:
        # Synchronous publish — called from the asyncio loop. Drops events
        # to slow subscribers rather than blocking the pipeline.
        self.total_published += 1
        for sub in list(self._subs):
            try:
                sub.q.put_nowait(payload)
                sub.published += 1
                sub.consecutive_drops = 0
            except asyncio.QueueFull:
                sub.dropped += 1
                sub.consecutive_drops += 1
                self.total_dropped += 1
                if (sub.consecutive_drops == self.DROP_WARN_THRESHOLD
                        and sub.consecutive_drops != sub.last_drop_warned):
                    log.warning("status: client '%s' dropped %d events in a row "
                                "(queue full — slow consumer?)",
                                sub.label, sub.consecutive_drops)
                    sub.last_drop_warned = sub.consecutive_drops

    def metrics(self) -> Dict[str, Any]:
        return {
            "total_published": self.total_published,
            "total_dropped": self.total_dropped,
            "subscribers": [
                {
                    "label": s.label,
                    "published": s.published,
                    "dropped": s.dropped,
                    "queue_depth": s.q.qsize(),
                }
                for s in self._subs
            ],
        }


class TelemetryParser:
    """Regex-based parser for the firmware's existing DIAG/TELEMETRY/VTC_RX
    lines. Maps captured fields to catalog status.* ids and publishes deltas.

    The parser keeps the last value per id and only republishes on change —
    no point sending the same S2MM_SR every second."""

    # The firmware DIAG line wraps each SR with a bracketed bitfield decode,
    # e.g. S2MM_SR=0x00011810[FrmCnt  frmcnt=1]. The bracket content contains
    # spaces, so match it with [^\]]* rather than \S*.
    RE_DIAG = re.compile(
        r"DIAG:\s*h_in=(\d+)\s+v_in=(\d+)\s+v_emit=(\d+)\s+v_out_tlast=(\d+)\s+"
        r"S2MM_SR=(0x[0-9a-fA-F]+)(?:\[[^\]]*\])?\s+"
        r"MM2S_SR=(0x[0-9a-fA-F]+)(?:\[[^\]]*\])?\s+"
        r"RDSTORE=(\d+)\s+WRSTORE=(\d+)\s+src=(\d+)\s+out=(\d+)")
    RE_TELEMETRY = re.compile(
        r"TELEMETRY:\s+src=([\d.]+)\s+Hz\s+->\s+regime\s+(\d+)\s+\[(.+?)\]")
    RE_VTCRX = re.compile(
        r"VTC_RX:\s+HACTIVE=(\d+)\s+VACTIVE=(\d+)\s+HTOTAL=(\d+)\s+VTOTAL=(\d+)")
    RE_LOCKED = re.compile(r"dvi2rgb pLocked stable")

    def __init__(self, bus: StatusBus):
        self.bus = bus
        self.last: Dict[str, Any] = {}
        # Output format is a build-time constant for v0.1 — bag it from the
        # banner line and reuse.
        self._output_format = "720p60"  # default until banner says otherwise

    def feed(self, line: str) -> None:
        try:
            self._feed(line)
        except Exception as e:
            log.warning("telemetry parser error: %s on line %r", e, line)

    def _feed(self, line: str) -> None:
        if m := self.RE_DIAG.search(line):
            self._update("status.s2mm_sr", int(m.group(5), 16))
            self._update("status.mm2s_sr", int(m.group(6), 16))
            # DIAG only fires once the pipeline is locked, so its presence
            # implies source_lock=true. src/out are integer-Hz approximations
            # adequate for the operator status bar.
            self._update("status.source_lock", True)
            self._update("status.source_rate_hz", int(m.group(9)))
            self._update("status.output_rate_hz", int(m.group(10)))
            return
        if m := self.RE_TELEMETRY.search(line):
            hz = float(m.group(1))
            regime_lbl = m.group(3)
            self._update("status.source_rate_hz", round(hz, 3))
            self._update("status.regime", regime_lbl)
            return
        if m := self.RE_VTCRX.search(line):
            hactive = int(m.group(1)); vactive = int(m.group(2))
            self._update("status.source_format", f"{hactive}x{vactive}")
            self._update("status.source_lock", True)
            return
        if self.RE_LOCKED.search(line):
            self._update("status.source_lock", True)
            return
        if "VTC: configuring 720p60" in line:
            self._output_format = "720p60"
            self._update("status.output_format", "720p60")
        elif "VTC: configuring 1080p30" in line:
            self._output_format = "1080p30"
            self._update("status.output_format", "1080p30")
        elif "VTC: configuring 1080p60" in line:
            self._output_format = "1080p60"
            self._update("status.output_format", "1080p60")

    def _update(self, cid: str, value: Any) -> None:
        if self.last.get(cid) == value:
            return
        self.last[cid] = value
        # Publish as a JSON-RPC notification (no id). Web UI handler routes
        # status.update notifications into the per-row value cells.
        self.bus.publish({
            "jsonrpc": "2.0",
            "method": "status.update",
            "params": {"id": cid, "value": value},
        })


# ---------------------------------------------------------------------------
# JSON-RPC dispatcher — handles methods coming from WebSocket clients
# ---------------------------------------------------------------------------

class Dispatcher:
    def __init__(self, catalog: Catalog, uart: UartBridge, profiles: ProfileStore,
                 bus: "StatusBus"):
        self.catalog = catalog
        self.uart = uart
        self.profiles = profiles
        self.bus = bus
        self.methods: Dict[str, Callable[[Dict[str, Any]], Awaitable[Any]]] = {
            "system.identify":      self._m_identify,
            "system.catalog":       self._m_catalog,
            "system.list_controls": self._m_list_controls,
            "control.get":          self._m_control_get,
            "control.set":          self._m_control_set,
            "profile.list":         self._m_profile_list,
            "profile.load":         self._m_profile_load,
            "profile.save":         self._m_profile_save,
            "status.snapshot":      self._m_status_snapshot,
            "system.metrics":       self._m_system_metrics,
            "debug.dump":           self._m_debug_dump,
            "geom.set":             self._m_geom_set,
            "warp.set":             self._m_warp_set,
            "blend.set":            self._m_blend_set,
            "operator.set":         self._m_operator_set,
            "arc.set":              self._m_arc_set,
            "gamma.set":            self._m_gamma_set,
            "colorspace.set":       self._m_colorspace_set,
        }
        self.telemetry: Optional[TelemetryParser] = None  # set by daemon main

    async def handle(self, req: Dict[str, Any]) -> Dict[str, Any]:
        rid = req.get("id")
        method = req.get("method")
        params = req.get("params") or {}
        if method not in self.methods:
            return _error(rid, -32601, f"unknown method '{method}'")
        try:
            result = await self.methods[method](params)
            return {"jsonrpc": "2.0", "id": rid, "result": result}
        except ValueError as e:
            return _error(rid, -32602, str(e))
        except KeyError as e:
            return _error(rid, -32602, f"missing param: {e}")
        except Exception as e:
            log.exception("dispatcher: %s failed", method)
            return _error(rid, -32603, str(e))

    async def _m_identify(self, params: Dict[str, Any]) -> Dict[str, Any]:
        try:
            fw = await self.uart.request("system.identify")
            fw_result = fw.get("result", {})
        except Exception as e:
            fw_result = {"error": str(e)}
        return {
            "daemon": "schindlerd",
            "daemon_version": "0.1.0",
            "catalog": self.catalog.version,
            "firmware": fw_result,
        }

    async def _m_catalog(self, params: Dict[str, Any]) -> Dict[str, Any]:
        if self.catalog.available_ids is None:
            await self.probe_firmware_controls()
        return self.catalog.annotated_raw()

    async def probe_firmware_controls(self) -> None:
        """Ask the firmware which controls it actually implements. Used to
        annotate the catalog so the UI can hide gated controls."""
        try:
            fw = await self.uart.request("system.list_controls")
            ids = fw.get("result", {}).get("ids", [])
            self.catalog.available_ids = set(ids)
            log.info("firmware reports %d available controls", len(ids))
        except Exception as e:
            log.warning("firmware probe failed: %s", e)
            self.catalog.available_ids = set()

    async def _m_list_controls(self, params: Dict[str, Any]) -> List[str]:
        return list(self.catalog.controls.keys())

    async def _m_control_get(self, params: Dict[str, Any]) -> Dict[str, Any]:
        cid = params["id"]
        ctl = self.catalog.controls.get(cid)
        if ctl is None:
            raise ValueError(f"unknown control id '{cid}'")
        fw = await self.uart.request("control.get", {"id": cid})
        if "error" in fw:
            raise RuntimeError(f"firmware: {fw['error'].get('message', '?')}")
        raw_val = fw["result"]["value"]
        return {"id": cid, "value": ctl.coerce_from_firmware(raw_val)}

    async def _m_control_set(self, params: Dict[str, Any]) -> Dict[str, Any]:
        cid = params["id"]
        ctl = self.catalog.controls.get(cid)
        if ctl is None:
            raise ValueError(f"unknown control id '{cid}'")
        if ctl.read_only:
            raise ValueError(f"'{cid}' is read-only")
        fw_val = ctl.coerce_to_firmware(params["value"])
        fw = await self.uart.request("control.set", {"id": cid, "value": fw_val})
        if "error" in fw:
            raise RuntimeError(f"firmware: {fw['error'].get('message', '?')}")
        raw_val = fw["result"]["value"]
        out_val = ctl.coerce_from_firmware(raw_val)
        # Multi-client coordination: every connected client receives a
        # control.changed notification so all open browsers stay in sync.
        # The originating client filters its own echo via inflight/pending
        # state in the UI handler.
        self.bus.publish({
            "jsonrpc": "2.0",
            "method": "control.changed",
            "params": {"id": cid, "value": out_val},
        })
        return {"id": cid, "value": out_val}

    async def _m_warp_set(self, params: Dict[str, Any]) -> Dict[str, Any]:
        """Warp read-engine geometry: rotation + zoom, sent COHERENTLY as one raw
        'W <deg> <invx> <invy>' (WARP build only; not a catalog control). The daemon holds the
        current (deg, invx, invy) so changing zoom preserves rotation and vice-versa — unlike the
        route-B 'G' command, which writes the same GPIOs as the warp coeffs and would clobber them.
          deg          : -180..180 (firmware wraps mod 360, auto per-geometry LEAD)
          invx/invy    : inverse scale, Q12 (4096 = 1:1; >4096 = zoom OUT/downscale; <4096 = zoom IN)
          zoom         : convenience % (100 = 1:1; 200 = 2x zoom-in); maps to invx=invy=4096*100/zoom"""
        if not hasattr(self, "_warp_deg"):
            self._warp_deg, self._warp_invx, self._warp_invy = 0, 4096, 4096
            self._warp_panx = self._warp_pany = 0
        if "deg" in params:
            d = int(round(float(params["deg"])))
            while d > 180:  d -= 360
            while d < -180: d += 360
            self._warp_deg = d
        def cl(v): return 256 if v < 256 else 0xFFFFF if v > 0xFFFFF else v
        if "invx" in params: self._warp_invx = cl(int(round(float(params["invx"]))))
        if "invy" in params: self._warp_invy = cl(int(round(float(params["invy"]))))
        if "zoom" in params:
            z = max(25.0, min(400.0, float(params["zoom"])))
            iv = cl(int(round(4096.0 * 100.0 / z)))
            self._warp_invx = self._warp_invy = iv
        if "panx" in params: self._warp_panx = int(round(float(params["panx"])))
        if "pany" in params: self._warp_pany = int(round(float(params["pany"])))
        self.uart.send_raw(f"W {self._warp_deg} {self._warp_invx} {self._warp_invy} {self._warp_panx} {self._warp_pany}")
        out = {"deg": self._warp_deg, "invx": self._warp_invx, "invy": self._warp_invy,
               "panx": self._warp_panx, "pany": self._warp_pany}
        self.bus.publish({"jsonrpc": "2.0", "method": "warp.changed", "params": out})
        return out

    async def _m_geom_set(self, params: Dict[str, Any]) -> Dict[str, Any]:
        """Read-engine geometry: scale w×h, SIGNED shift (x,y), anchor mode.
        Sent as the raw 'G w h x y a' firmware command (not a catalog control).
          w,h    : scaled image size in output-raster px (1280/720 = 100%, up to 200%)
          x,y    : SIGNED shift in output px (+right/down, -left/up); may push the image
                   off the edge — pixels then leave the frame and matte fills the opposite side
          anchor : 0 = scale about image center (default), 1 = top-left corner
        Firmware derives the on-screen window position + source-crop seed; the daemon just
        clamps and forwards, then broadcasts geom.changed for multi-client sync."""
        def clampi(v: Any, lo: int, hi: int) -> int:
            iv = int(round(float(v)))
            return lo if iv < lo else hi if iv > hi else iv
        # scale up to 300% of the 720p output raster (3840x2160); firmware clamps to 3× too.
        w = clampi(params.get("w", 1280), 1, 3840)
        h = clampi(params.get("h", 720), 1, 2160)
        # signed shift; range lets the image be pushed fully off-screen at 100%.
        x = clampi(params.get("x", 0), -2560, 2560)
        y = clampi(params.get("y", 0), -1440, 1440)
        anchor = 1 if params.get("anchor", 0) else 0
        filt = clampi(params.get("filt", 0), 0, 3)  # #107: 0=NN 1=2-tap box 2=H-bilinear 3=H+V-bilinear
        hflip = 1 if params.get("hflip", 0) else 0
        vflip = 1 if params.get("vflip", 0) else 0  # 180° = both
        # Only emit the flip command when it actually changes — otherwise every size/shift
        # drag would do a redundant 2nd full geometry write (P then G), doubling the
        # multi-register GPIO churn and the chance a frame-latch samples a half-written update.
        if getattr(self, "_last_flip", None) != (hflip, vflip):
            self.uart.send_raw(f"P {hflip} {vflip}")
            self._last_flip = (hflip, vflip)
        self.uart.send_raw(f"G {w} {h} {x} {y} {anchor} {filt}")
        applied = {"w": w, "h": h, "x": x, "y": y, "anchor": anchor, "filt": filt,
                   "hflip": hflip, "vflip": vflip}
        self.bus.publish({"jsonrpc": "2.0", "method": "geom.changed", "params": applied})
        return applied

    async def _m_blend_set(self, params: Dict[str, Any]) -> Dict[str, Any]:
        """Mackin blend mode (read-engine). Raw 'M 0|1|2': 0=off (drop/repeat),
        1=intelligent (blend mid-phase), 2=force (blend every interframe). Accepts
        {"mode":0|1|2} or legacy {"enabled":bool}. Not a catalog control."""
        if "mode" in params:
            m = int(params["mode"]); m = 0 if m < 0 else 2 if m > 2 else m
        else:
            m = 1 if params.get("enabled") else 0
        self.uart.send_raw(f"M {m}")
        self.bus.publish({"jsonrpc": "2.0", "method": "blend.changed", "params": {"mode": m}})
        return {"mode": m}

    async def _m_operator_set(self, params: Dict[str, Any]) -> Dict[str, Any]:
        """Operator quick-actions (parity Phase 1) — raw 'O ...' firmware commands. Any of:
        {"mono":0|1} {"bypass":0|1} {"black":0|1} {"temp":<K>} {"fade":<0-255>,"step":<n>}."""
        out: Dict[str, Any] = {}
        if "mono" in params:
            m = 1 if params["mono"] else 0; self.uart.send_raw(f"O m {m}"); out["mono"] = m
        if "bypass" in params:
            y = 1 if params["bypass"] else 0; self.uart.send_raw(f"O y {y}"); out["bypass"] = y
        if "black" in params:
            k = 1 if params["black"] else 0; self.uart.send_raw(f"O k {k}"); out["black"] = k
        if "freeze" in params:
            z = 1 if params["freeze"] else 0; self.uart.send_raw(f"O z {z}"); out["freeze"] = z
        if "gamma" in params:
            g = int(params["gamma"]); self.uart.send_raw(f"O g {g}"); out["gamma"] = g  # 0=off,18,22,24
        if "temp" in params:
            t = int(params["temp"]); self.uart.send_raw(f"O t {t}"); out["temp"] = t
        if "fade" in params:
            tgt = int(params["fade"]); tgt = 0 if tgt < 0 else 255 if tgt > 255 else tgt
            step = int(params.get("step", 6)); step = 1 if step < 1 else step
            self.uart.send_raw(f"O f {tgt} {step}"); out["fade"] = tgt
        self.bus.publish({"jsonrpc": "2.0", "method": "operator.changed", "params": out})
        return out

    # ARC (aspect) modes — preset window sizes on the signed-window geometry engine; the
    # engine centers (anchor=0) and mattes the rest. Pure geometry preset, no firmware/HDL.
    # NOTE: scales the full source into the window, so the cross-aspect modes (4:3/letterbox)
    # change the picture's aspect (anamorphic) for a 16:9 source — the operator framing tool.
    _ARC_TABLE = {
        "fill":      (1280, 720),   # 16:9 fill (default)
        "zoom":      (1408, 792),   # ~110% overscan, undistorted (crops edges)
        "4:3":       (960,  720),   # pillarbox (bars L/R)
        "14:9":      (1120, 720),   # 14:9 compromise
        "letterbox": (1280, 545),   # 2.35:1 letterbox (bars T/B)
    }

    async def _m_arc_set(self, params: Dict[str, Any]) -> Dict[str, Any]:
        """Aspect-ratio preset: fill / zoom / 4:3 / 14:9 / letterbox. Sets a centered window
        of the preset size on the geometry engine (preserves the current flip state)."""
        mode = str(params.get("mode", "fill"))
        w, h = self._ARC_TABLE.get(mode, self._ARC_TABLE["fill"])
        lf = getattr(self, "_last_flip", (0, 0))
        res = await self._m_geom_set({"w": w, "h": h, "x": 0, "y": 0, "anchor": 0,
                                      "hflip": lf[0], "vflip": lf[1]})
        self.bus.publish({"jsonrpc": "2.0", "method": "arc.changed", "params": {"mode": mode}})
        return {"mode": mode, **res}

    async def _m_gamma_set(self, params: Dict[str, Any]) -> Dict[str, Any]:
        """Continuous gamma (0.1 steps). The firmware computes the curve on-device from
        gamma*10 (fixed-point, verified ≤1 LSB vs pow), so we send only the short value
        'O g <gamma*10>' — no bulk LUT transport. g<=0 or 1.0 → off/linear."""
        g = float(params.get("gamma", 1.0))
        gx10 = int(round(g * 10.0))
        if gx10 < 0:
            gx10 = 0
        self.uart.send_raw(f"O g {gx10}")
        self.bus.publish({"jsonrpc": "2.0", "method": "gamma.changed", "params": {"gamma": g}})
        return {"gamma": g}

    async def _m_colorspace_set(self, params: Dict[str, Any]) -> Dict[str, Any]:
        """Input colorspace override (parity 3.5). {range: 'full'|'limited'} via color_correct
        black/white preset ('C r 0|1'). YCbCr→RGB matrix decode is deferred (needs a YCbCr
        source to validate the TMDS lane order before shipping the coefficients)."""
        out: Dict[str, Any] = {}
        if "range" in params:
            r = 1 if str(params["range"]).lower().startswith("lim") else 0
            self.uart.send_raw(f"C r {r}")
            out["range"] = "limited" if r else "full"
        self.bus.publish({"jsonrpc": "2.0", "method": "colorspace.changed", "params": out})
        return out

    async def _m_profile_list(self, params: Dict[str, Any]) -> List[str]:
        return self.profiles.list()

    async def _m_profile_load(self, params: Dict[str, Any]) -> Dict[str, Any]:
        name = params["name"]
        prof = self.profiles.load(name)
        # Reject profiles whose catalog_version major differs from ours.
        # Minor mismatches still apply best-effort. See CATALOG-EVOLUTION.md.
        prof_v = prof.get("catalog_version", "0.0.0")
        try:
            prof_major = int(prof_v.split(".")[0])
            live_major = int(self.catalog.version.split(".")[0])
        except (ValueError, IndexError):
            prof_major = live_major = 0
        if prof_major != live_major:
            raise ValueError(
                f"catalog major-version mismatch: profile '{name}' authored "
                f"against catalog {prof_v}, daemon serving {self.catalog.version}")
        applied = []
        skipped = []
        for cid, value in prof.get("controls", {}).items():
            try:
                await self._m_control_set({"id": cid, "value": value})
                applied.append(cid)
            except Exception as e:
                log.warning("profile '%s': %s failed: %s", name, cid, e)
                skipped.append({"id": cid, "reason": str(e)})
        return {"name": name, "applied": applied, "skipped": skipped}

    async def _m_profile_save(self, params: Dict[str, Any]) -> Dict[str, Any]:
        name = params["name"]
        # If caller passed an explicit controls dict, save that. Otherwise read
        # back the current state of every settable control.
        if "controls" in params:
            controls = params["controls"]
        else:
            controls = {}
            for cid, ctl in self.catalog.controls.items():
                if ctl.read_only or ctl.type == "trigger":
                    continue
                try:
                    r = await self._m_control_get({"id": cid})
                    controls[cid] = r["value"]
                except Exception as e:
                    log.warning("profile.save: skipping %s (%s)", cid, e)
        profile = {
            "schema": "schindler-profile",
            "schema_version": "0.1.0",
            "catalog_version": self.catalog.version,
            "name": name,
            "controls": controls,
        }
        self.profiles.save(name, profile)
        return {"name": name, "saved": len(controls)}

    async def _m_system_metrics(self, params: Dict[str, Any]) -> Dict[str, Any]:
        """Daemon health: bus pub/drop counts + per-client queue depths.
        Useful when diagnosing whether a slow client is causing event drops."""
        return self.bus.metrics()

    async def _m_debug_dump(self, params: Dict[str, Any]) -> Dict[str, Any]:
        """DDR framebuffer dump (scaler-testing instrument). Forwards to the
        firmware debug.dump J method with a long timeout — dumps stream ~10-20 KB
        of base64 over UART (1-4 s). Pass-through of {mode,slot,w,h,fmt,data}."""
        fw = await self.uart.request("debug.dump", params or {}, timeout=12.0)
        if "error" in fw:
            raise RuntimeError(f"firmware: {fw['error'].get('message', '?')}")
        return fw["result"]

    async def _m_status_snapshot(self, params: Dict[str, Any]) -> Dict[str, Any]:
        """Return the current value of every status field the daemon has seen.
        Clients call this after their UI has rendered so they can populate the
        status panel from cached state — works around the race between the WS
        connect-time snapshot replay (sent immediately) and the browser's
        catalog-render path (which takes ~100ms to populate its row table)."""
        if self.telemetry is None:
            return {}
        return dict(self.telemetry.last)


def _error(rid: Any, code: int, message: str) -> Dict[str, Any]:
    return {"jsonrpc": "2.0", "id": rid, "error": {"code": code, "message": message}}


# ---------------------------------------------------------------------------
# WebSocket server
# ---------------------------------------------------------------------------

async def ws_handler(ws: "WebSocketServerProtocol", dispatcher: Dispatcher,
                     auth_token: Optional[str] = None) -> None:
    log.info("ws: client connected from %s", getattr(ws, "remote_address", "?"))

    # Auth handshake (Risk N1 prep). When auth_token is set, the first frame
    # MUST be a system.auth request with the matching token. Anything else
    # gets a -32001 "unauthorized" and the connection closes. Default is
    # None (disabled) — preserves today's localhost-only convenience.
    if auth_token is not None:
        try:
            first = await asyncio.wait_for(ws.recv(), timeout=5.0)
            req = json.loads(first)
            if (req.get("method") != "system.auth"
                    or req.get("params", {}).get("token") != auth_token):
                await ws.send(json.dumps(_error(req.get("id"), -32001,
                                                "unauthorized")))
                await ws.close()
                log.warning("ws: client failed auth from %s",
                            getattr(ws, "remote_address", "?"))
                return
            await ws.send(json.dumps({
                "jsonrpc": "2.0", "id": req.get("id"),
                "result": {"authorized": True},
            }))
        except (asyncio.TimeoutError, json.JSONDecodeError):
            await ws.close()
            return

    # Subscribe this client to the status bus. A background task drains the
    # queue and forwards each event as a JSON notification.
    addr = getattr(ws, "remote_address", None)
    label = f"{addr[0]}:{addr[1]}" if addr else "ws-client"
    sub = await dispatcher.bus.subscribe(label=label)
    push_task = asyncio.create_task(_drain_status_to_ws(sub.q, ws))
    # Replay last-known status snapshot so a fresh client doesn't have to
    # wait up to ~1s for the next DIAG line.
    try:
        for cid, val in list(dispatcher.telemetry.last.items()):
            await ws.send(json.dumps({
                "jsonrpc": "2.0",
                "method": "status.update",
                "params": {"id": cid, "value": val},
            }))
    except Exception:
        pass
    try:
        async for raw in ws:
            try:
                req = json.loads(raw)
            except json.JSONDecodeError:
                await ws.send(json.dumps(_error(None, -32700, "parse error")))
                continue
            resp = await dispatcher.handle(req)
            await ws.send(json.dumps(resp))
    except websockets.ConnectionClosed:
        pass
    finally:
        push_task.cancel()
        await dispatcher.bus.unsubscribe(sub)
        log.info("ws: client disconnected")


async def _drain_status_to_ws(q: asyncio.Queue, ws) -> None:
    try:
        while True:
            payload = await q.get()
            try:
                await ws.send(json.dumps(payload))
            except websockets.ConnectionClosed:
                return
    except asyncio.CancelledError:
        return


# ---------------------------------------------------------------------------
# Minimal HTTP static server (serves the web UI from ../web/)
# ---------------------------------------------------------------------------

async def http_handler(reader: asyncio.StreamReader, writer: asyncio.StreamWriter,
                       web_root: Path) -> None:
    try:
        request_line = await reader.readline()
        if not request_line:
            writer.close(); return
        parts = request_line.decode("ascii", "replace").split()
        if len(parts) < 2 or parts[0] != "GET":
            writer.write(b"HTTP/1.1 405 Method Not Allowed\r\nContent-Length:0\r\n\r\n")
            await writer.drain(); writer.close(); return
        path = parts[1]
        # Drain headers
        while True:
            line = await reader.readline()
            if line in (b"\r\n", b"\n", b""):
                break
        if path == "/" or path == "":
            path = "/index.html"
        # Strip leading slash, prevent traversal
        safe = path.lstrip("/").replace("..", "")
        f = web_root / safe
        if not f.is_file():
            body = b"<h1>404</h1>schindlerd: not found"
            writer.write(b"HTTP/1.1 404 Not Found\r\nContent-Type:text/html\r\n"
                         + f"Content-Length:{len(body)}\r\n\r\n".encode() + body)
        else:
            body = f.read_bytes()
            ctype = {
                ".html": "text/html",
                ".js":   "application/javascript",
                ".css":  "text/css",
                ".json": "application/json",
            }.get(f.suffix, "application/octet-stream")
            writer.write(b"HTTP/1.1 200 OK\r\n"
                         + f"Content-Type:{ctype}\r\nContent-Length:{len(body)}\r\n\r\n".encode()
                         + body)
        await writer.drain()
    except Exception as e:
        log.warning("http: %s", e)
    finally:
        try: writer.close()
        except Exception: pass


# ---------------------------------------------------------------------------
# Main
# ---------------------------------------------------------------------------

async def amain(args: argparse.Namespace) -> int:
    catalog_path = Path(args.catalog).resolve()
    if not catalog_path.is_file():
        log.error("catalog not found: %s", catalog_path)
        return 2
    catalog = Catalog.load(catalog_path)
    log.info("catalog: v%s with %d controls", catalog.version, len(catalog.controls))

    uart = UartBridge(args.port, args.baud)
    uart.start(asyncio.get_running_loop())

    bus = StatusBus()
    telemetry = TelemetryParser(bus)
    uart.text_log_handler = telemetry.feed

    profiles = ProfileStore(
        Path(args.profiles).expanduser(),
        readonly_roots=[Path(args.factory_profiles).resolve()] if args.factory_profiles else None,
    )
    dispatcher = Dispatcher(catalog, uart, profiles, bus)
    dispatcher.telemetry = telemetry  # exposed to ws_handler for snapshot replay

    web_root = Path(args.web).resolve() if args.web else None
    if web_root and not web_root.is_dir():
        log.warning("web root not found, HTTP disabled: %s", web_root)
        web_root = None

    auth_token = os.environ.get("SCHINDLERD_AUTH_TOKEN") or None
    if auth_token:
        log.info("ws: auth ENABLED (SCHINDLERD_AUTH_TOKEN set)")
    elif args.host != "127.0.0.1" and args.host != "localhost":
        log.warning("ws: binding non-loopback (%s) without auth — "
                    "Risk N1 release-gate. Set SCHINDLERD_AUTH_TOKEN.",
                    args.host)
    ws_server = await websockets.serve(
        lambda ws: ws_handler(ws, dispatcher, auth_token=auth_token),
        host=args.host, port=args.ws_port,
    )
    log.info("ws: serving on ws://%s:%d", args.host, args.ws_port)

    http_server = None
    if web_root:
        http_server = await asyncio.start_server(
            lambda r, w: http_handler(r, w, web_root),
            host=args.host, port=args.http_port,
        )
        log.info("http: serving %s on http://%s:%d", web_root, args.host, args.http_port)

    try:
        await asyncio.Future()  # run forever
    except (asyncio.CancelledError, KeyboardInterrupt):
        pass
    finally:
        uart.stop()
        ws_server.close()
        await ws_server.wait_closed()
        if http_server:
            http_server.close()
            await http_server.wait_closed()
    return 0


def main() -> int:
    p = argparse.ArgumentParser(prog="schindlerd")
    p.add_argument("--port",      default="/dev/ttyUSB1", help="serial device")
    p.add_argument("--baud",      type=int, default=115200)
    p.add_argument("--catalog",   default=os.path.join(os.path.dirname(__file__),
                                                       "..", "catalog-v0.2.0.json"))
    p.add_argument("--profiles",  default="~/.schindler/profiles")
    p.add_argument("--factory-profiles",
                   default=os.path.join(os.path.dirname(__file__),
                                        "..", "profiles", "factory"),
                   help="read-only profile dir shipped with the daemon")
    p.add_argument("--host",      default="127.0.0.1")
    p.add_argument("--ws-port",   type=int, default=8081)
    p.add_argument("--http-port", type=int, default=8080)
    p.add_argument("--web",       default=os.path.join(os.path.dirname(__file__), "..", "web"))
    p.add_argument("-v", "--verbose", action="count", default=0)
    args = p.parse_args()
    level = logging.WARNING - 10 * args.verbose
    logging.basicConfig(level=max(level, logging.DEBUG),
                        format="%(asctime)s %(name)s %(levelname)s: %(message)s")
    try:
        return asyncio.run(amain(args))
    except KeyboardInterrupt:
        return 0


if __name__ == "__main__":
    sys.exit(main())
