ibkickinit/schindler-clone/hdl/scaler_top.v

// scaler_top.v — top-level polyphase scaler. Wraps H + V cores into a
// single AXIS-in / AXIS-out block. Replaces scaler_passthrough in the BD.
//
// Build-time configurable: IN_W × IN_H input → OUT_W × OUT_H output, RGB
// 24-bit. C.1 first-light ran at 1920×1080 → 1280×720 (3:2 H, 3:2 V);
// C.2 makes that a generic. Internal AXIS between H and V is OUT_W × IN_H.
//
// Both stages run on the same input clock (PixelClk_in). VDMA's S2MM
// downstream of m_axis is on the same clock too — the dual-clock CDC
// happens later, between S2MM AXIS and MM2S AXIS via VDMA's internal
// frame buffer crossing.
//
// Downscale only for now: OUT_W <= IN_W and OUT_H <= IN_H. Upscale uses a
// different accumulator/emit policy (repeat input pixels, emit multiple
// per input) — not implemented; will be a separate code path when needed.

`default_nettype none
`timescale 1ns / 1ps

module scaler_top #(
    parameter integer IN_W_DEFAULT = 1920,
    parameter integer IN_H_DEFAULT = 1080,
    parameter integer OUT_W  = 1280,
    parameter integer OUT_H  =  720,
    parameter integer PHASES =   64,
    parameter integer TAPS_H =    8,
    parameter integer TAPS_V =    4
) (
    input  wire        aclk,
    input  wire        aresetn,

    input  wire [23:0] s_axis_tdata,
    input  wire        s_axis_tvalid,
    output wire        s_axis_tready,
    input  wire        s_axis_tlast,
    input  wire        s_axis_tuser,

    output wire [23:0] m_axis_tdata,
    output wire        m_axis_tvalid,
    input  wire        m_axis_tready,
    output wire        m_axis_tlast,
    output wire        m_axis_tuser,

    /* Runtime source dimensions from firmware via AXI GPIO. Driven on
     * FCLK_CLK0 (AXI clock) — CDC into aclk (PixelClk_in) below via 2-FF
     * synchronizers. For multi-bit values this is technically racy at the
     * instant of a write, but firmware writes once at startup (after VTC
     * detector lock) and re-writes only at source resolution change with
     * scaler held in soft reset — so we never sample a torn value in
     * steady state. */
    input  wire [15:0] in_w_async,
    input  wire [15:0] in_h_async,

    /* iter14 (2026-05-31): runtime kernel-mode select from AXI GPIO.
     *   [1:0] = kernel_mode_h_async
     *   [3:2] = kernel_mode_v_async
     * CDC'd into aclk inside scaler_top below. 4-bit slice from a 32-bit
     * GPIO; bits 31:4 reserved. Default = 4'b0101 → H=1, V=1 (production
     * 2-tap boxcar). Setting to 4'b0000 would give pure NN H+V. */
    input  wire [3:0]  kernel_mode_async,

    /* iter4g DIAG: per-frame counter snapshots (latched at TUSER inside the
     * scaler modules). Packed into a 48-bit bus for routing through the BD
     * to a CDC + AXI GPIO. Firmware reads via GPIO + prints via UART.
     *   [15:0]  = scaler_h input TLAST count per source frame
     *   [31:16] = scaler_v input TLAST count per source frame
     *   [47:32] = scaler_v emit (v_cross) count per source frame
     * All on aclk domain (pclk_in); CDC happens in top-level wiring. */
    output wire [47:0] diag_counts,
    /* iter5 (2026-05-22) DIAG: scaler_v m_axis_tlast handshake count per
     * source frame. Wired into BD's diag_concat/In1 slot (formerly the dead
     * axis_to_vid_io_0/mm2s_tlast_snap which always read 0). */
    output wire [15:0] out_tlast_snap
);
    /* 2-FF synchronizers on each bit. Marked ASYNC_REG for the placer. */
    (* ASYNC_REG = "TRUE" *) reg [15:0] in_w_q1, in_w_q2;
    (* ASYNC_REG = "TRUE" *) reg [15:0] in_h_q1, in_h_q2;
    /* iter14 kernel_mode CDC: 4-bit (2 bits per axis). Reset default
     * 4'b0101 = H mode 1 + V mode 1 = production 2-tap boxcar. */
    (* ASYNC_REG = "TRUE" *) reg [3:0]  km_q1, km_q2;
    always @(posedge aclk) begin
        if (!aresetn) begin
            in_w_q1 <= IN_W_DEFAULT[15:0]; in_w_q2 <= IN_W_DEFAULT[15:0];
            in_h_q1 <= IN_H_DEFAULT[15:0]; in_h_q2 <= IN_H_DEFAULT[15:0];
            km_q1   <= 4'b0101;            km_q2   <= 4'b0101;
        end else begin
            in_w_q1 <= in_w_async; in_w_q2 <= in_w_q1;
            in_h_q1 <= in_h_async; in_h_q2 <= in_h_q1;
            km_q1   <= kernel_mode_async; km_q2 <= km_q1;
        end
    end
    wire [1:0] kernel_mode_h = km_q2[1:0];
    wire [1:0] kernel_mode_v = km_q2[3:2];
    /* Zero-clamp: if firmware hasn't programmed valid dimensions yet (or GPIO
     * default applied wrong), substitute IN_W_DEFAULT / IN_H_DEFAULT so the
     * scaler's emit_now / v_cross math doesn't break. Without this, in_w==0
     * makes emit_now always true (every input pixel emits), which locks up
     * the AXIS pipeline and dies the HDMI output. */
    wire [11:0] in_w_eff = (in_w_q2 == 16'd0) ? IN_W_DEFAULT[11:0] : in_w_q2[11:0];
    wire [11:0] in_h_eff = (in_h_q2 == 16'd0) ? IN_H_DEFAULT[11:0] : in_h_q2[11:0];
    // Intermediate AXIS between H and V (OUT_W × IN_H)
    wire [23:0] mid_tdata;
    wire        mid_tvalid;
    wire        mid_tready;
    wire        mid_tlast;
    wire        mid_tuser;

    /* iter4g DIAG: counter wires from scaler_h and scaler_v, packed for
     * routing through the BD. All in aclk domain. Declared up front so
     * they're visible to the instances below. */
    wire [15:0] scaler_h_in_tlast_snap;
    wire [15:0] scaler_v_in_tlast_snap;
    wire [15:0] scaler_v_emit_snap;
    wire [15:0] scaler_v_out_tlast_snap;

    scaler_h #(
        .IN_W_DEFAULT (IN_W_DEFAULT),
        .OUT_W        (OUT_W),
        .PHASES       (PHASES),
        .TAPS         (TAPS_H)
    ) u_h (
        .clk           (aclk),
        .rstn          (aresetn),
        .s_axis_tdata  (s_axis_tdata),
        .s_axis_tvalid (s_axis_tvalid),
        .s_axis_tready (s_axis_tready),
        .s_axis_tlast  (s_axis_tlast),
        .s_axis_tuser  (s_axis_tuser),
        .m_axis_tdata  (mid_tdata),
        .m_axis_tvalid (mid_tvalid),
        .m_axis_tready (mid_tready),
        .m_axis_tlast  (mid_tlast),
        .m_axis_tuser  (mid_tuser),
        .in_w_runtime  (in_w_eff),
        .kernel_mode   (kernel_mode_h),
        .in_tlast_count_snap (scaler_h_in_tlast_snap)
    );

    scaler_v #(
        .IN_W         (OUT_W),
        .IN_H_DEFAULT (IN_H_DEFAULT),
        .OUT_H        (OUT_H),
        .PHASES       (PHASES),
        .TAPS         (TAPS_V)
    ) u_v (
        .clk           (aclk),
        .rstn          (aresetn),
        .s_axis_tdata  (mid_tdata),
        .s_axis_tvalid (mid_tvalid),
        .s_axis_tready (mid_tready),
        .s_axis_tlast  (mid_tlast),
        .s_axis_tuser  (mid_tuser),
        .m_axis_tdata  (m_axis_tdata),
        .m_axis_tvalid (m_axis_tvalid),
        .m_axis_tready (m_axis_tready),
        .m_axis_tlast  (m_axis_tlast),
        .m_axis_tuser  (m_axis_tuser),
        .in_h_runtime  (in_h_eff),
        .kernel_mode   (kernel_mode_v),
        .in_tlast_count_snap  (scaler_v_in_tlast_snap),
        .emit_count_snap      (scaler_v_emit_snap),
        .out_tlast_count_snap (scaler_v_out_tlast_snap)
    );

    assign diag_counts   = {scaler_v_emit_snap, scaler_v_in_tlast_snap, scaler_h_in_tlast_snap};
    assign out_tlast_snap = scaler_v_out_tlast_snap;
endmodule

`default_nettype wire
