ibkickinit/schindler-clone/hdl/axi_sync_inputs.v

// axi_sync_inputs.v — 2-FF synchronizers from various async domains into the
// AXI FCLK_CLK0 domain. Drives an AXI GPIO's gpio_io_i pins so firmware can
// poll source-side and output-side status for alignment and FRC.
//
// Phase D iter-3e (original): firmware-side VTC alignment via source vsync.
// Phase D iter-4d-1: added vsync_out and pclk_locked sync stages so firmware
// can count OUTPUT vsyncs (for cadence-driven PARK writes) and observe the
// output PixelClk MMCM lock directly.
//
// CDC: source vsync (~60 Hz), output vsync (~60 Hz), and both lock signals
// are slow-changing levels, so a plain 2-FF synchronizer is sufficient.

`default_nettype none
`timescale 1ns / 1ps

module axi_sync_inputs (
    input  wire axi_clk,                // FCLK_CLK0 (~100 MHz)
    input  wire axi_rstn,               // active-low reset, axi_clk domain

    input  wire vsync_async,            // dvi2rgb_0/vid_pVSync       (pclk_in)
    input  wire plocked_async,          // dvi2rgb_0/pLocked          (pclk_in)
    input  wire vsync_out_async,        // v_tc_tx/vsync_out          (pclk_out)
    input  wire pclk_locked_async,      // clk_wiz_pixclk_out/locked  (async)
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
